Maniak003/Anemometer/Documents/16.png

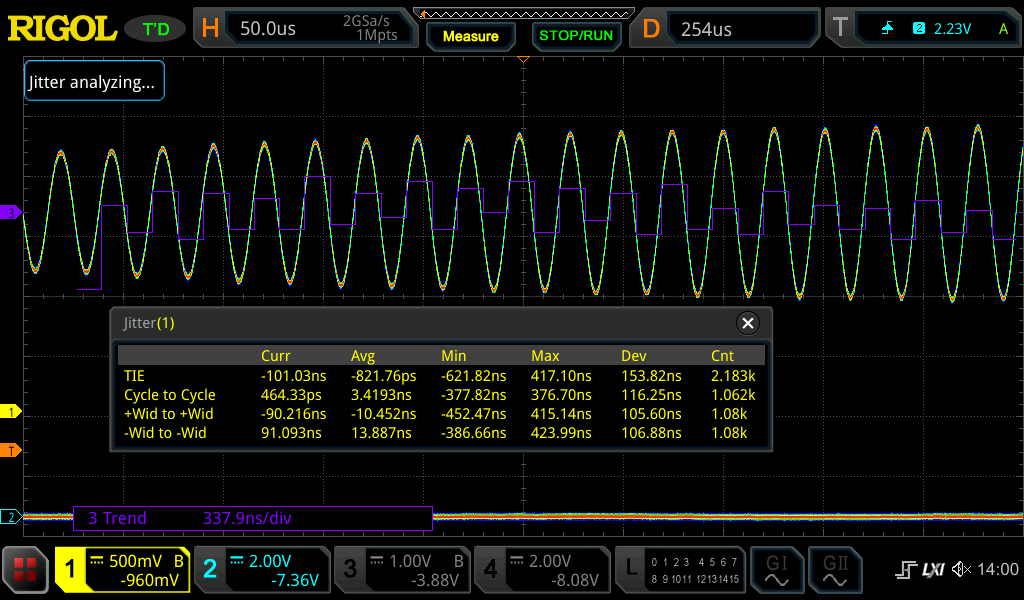
Documents/16.png
