Maniak003/Anemometer/Documents/29.png

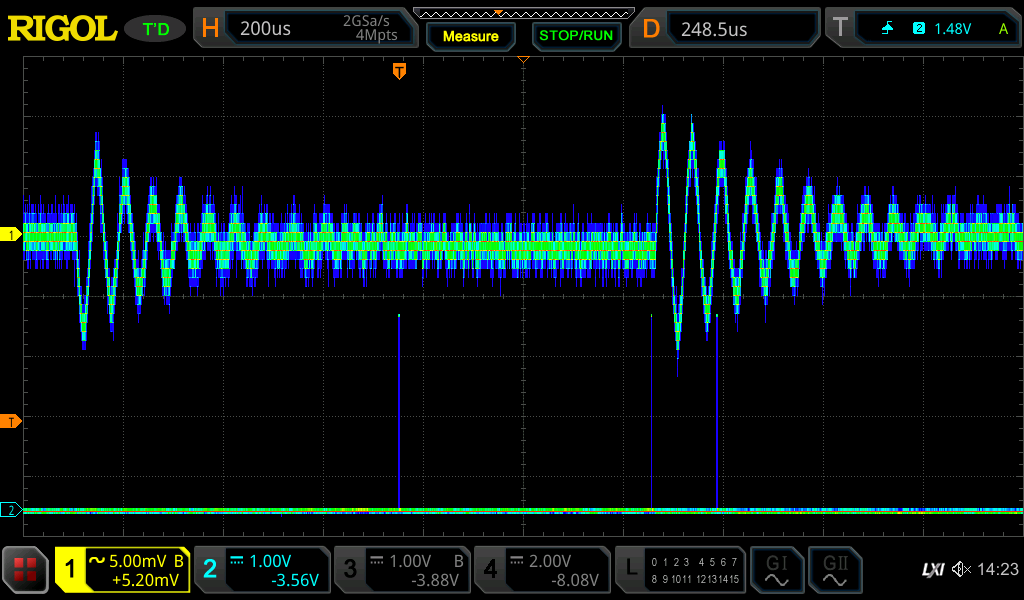
Documents/29.png
