Maniak003/Anemometer/Documents/34.png

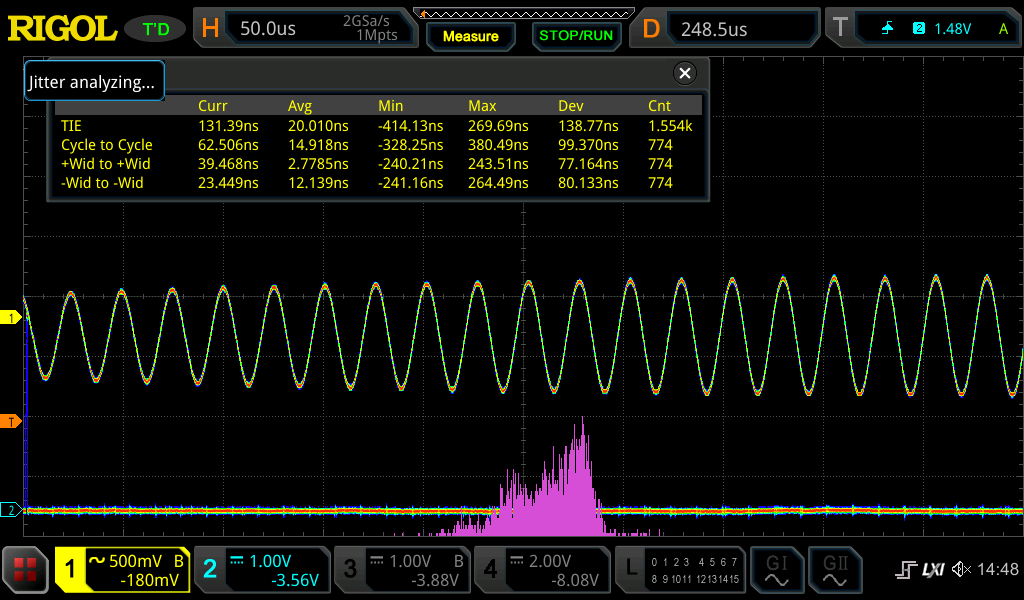
Documents/34.png
