Maniak003/Anemometer/Documents/63mm-Crystall_200khz.png

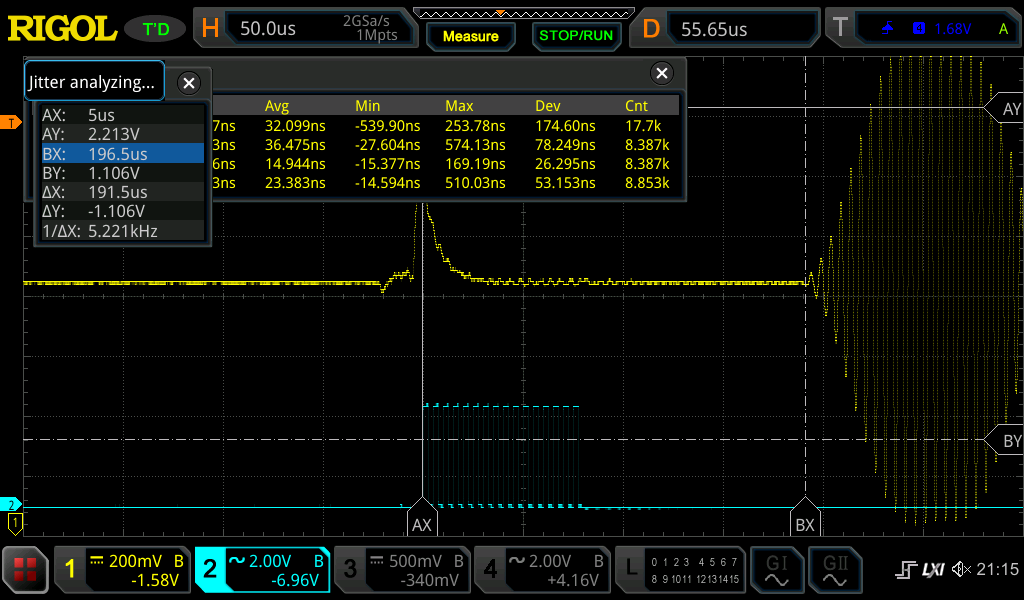
Documents/63mm-Crystall_200khz.png
