Maniak003/Anemometer/Documents/80.png

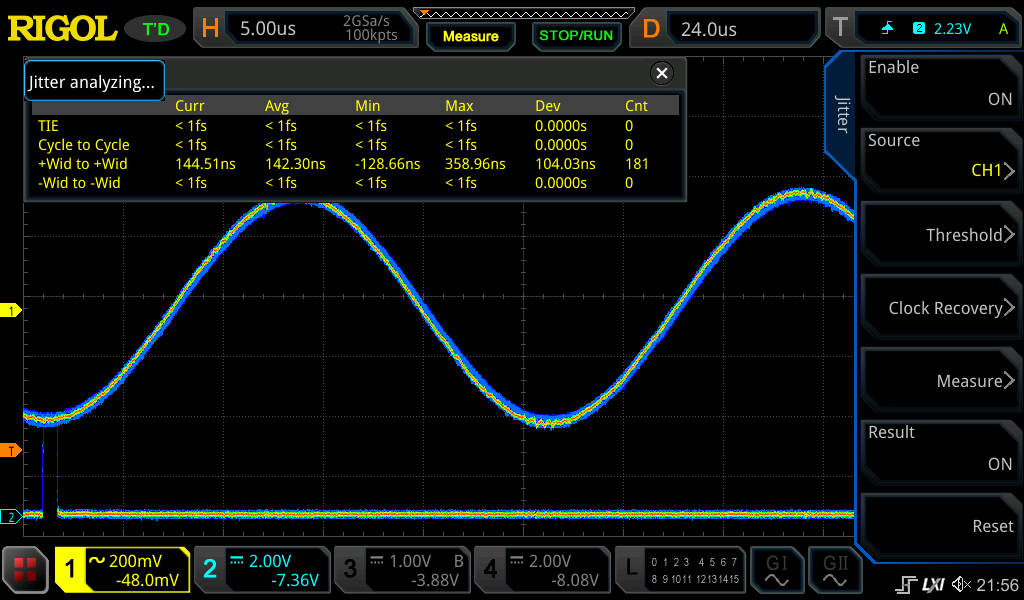
Documents/80.png
