Maniak003/Anemometer/Documents/200_conv.png

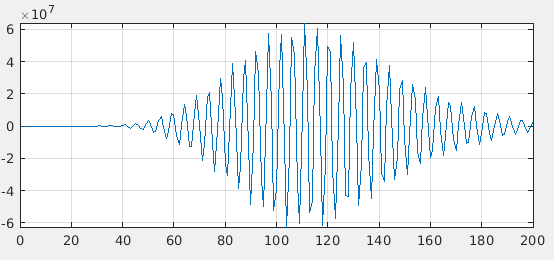
Documents/200_conv.png
