Maniak003/Anemometer/Documents/200_hilbert.png

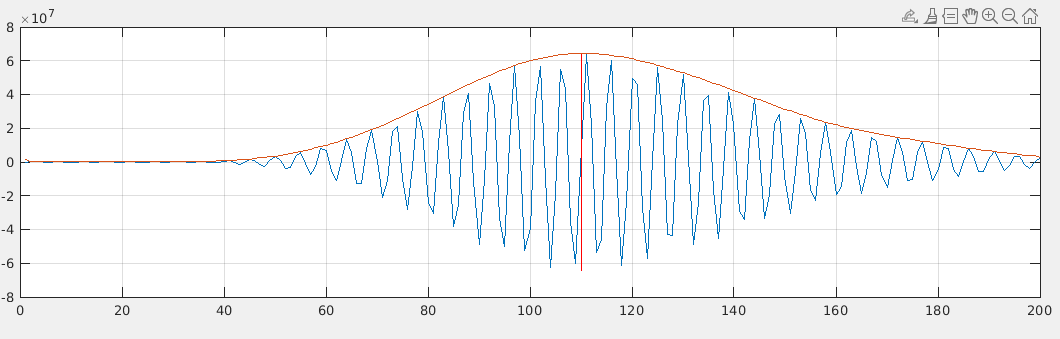
Documents/200_hilbert.png
