Maniak003/Anemometer/Documents/200_sample.png

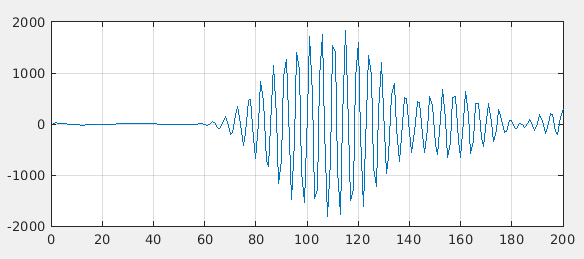
Documents/200_sample.png
