Maniak003/Anemometer/Documents/237.png

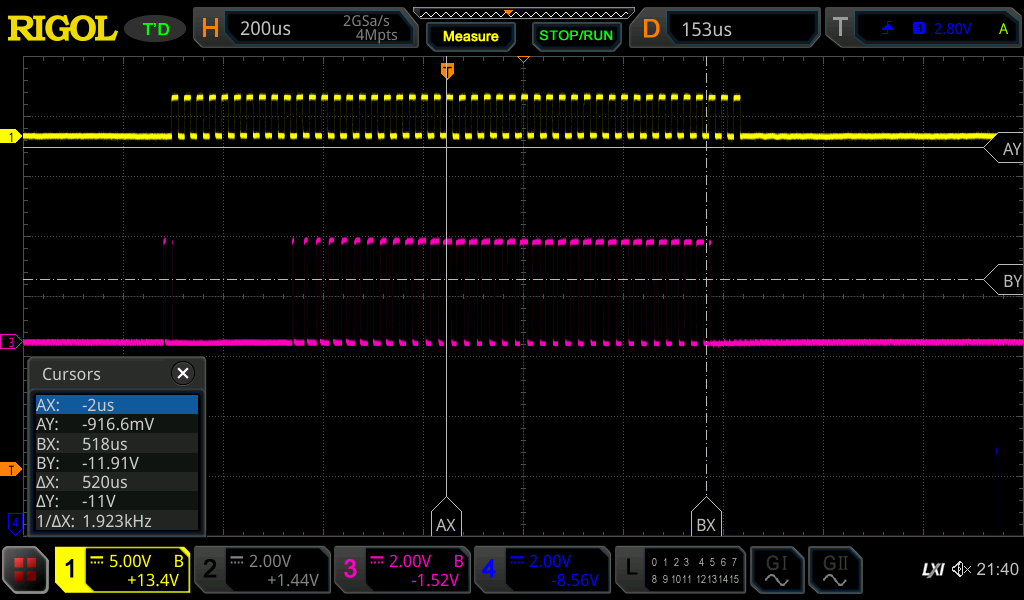
Documents/237.png
