Maniak003/Anemometer/Documents/344.png

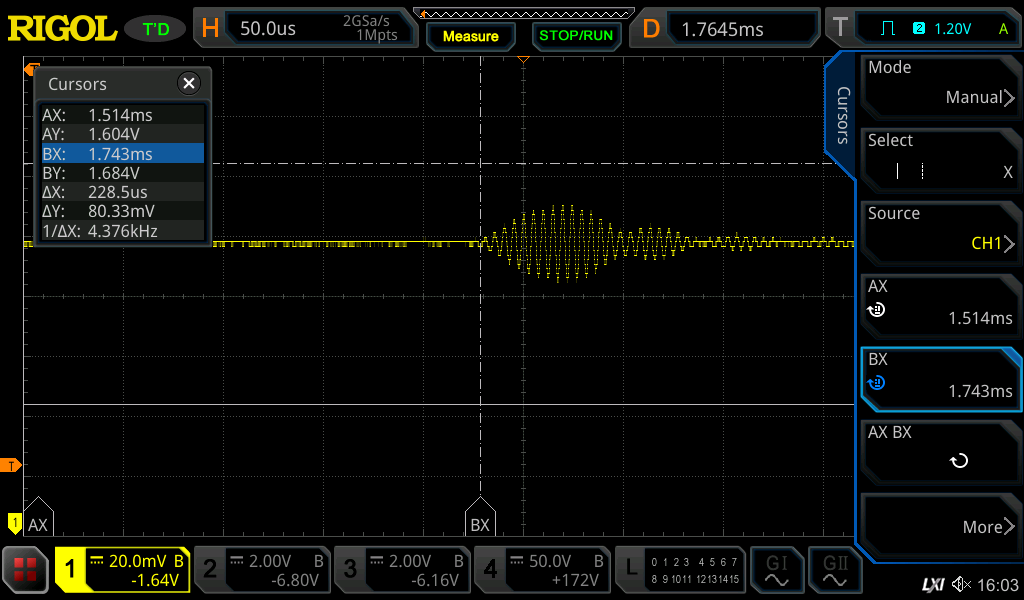
Documents/344.png
