Maniak003/Anemometer/Documents/406.png

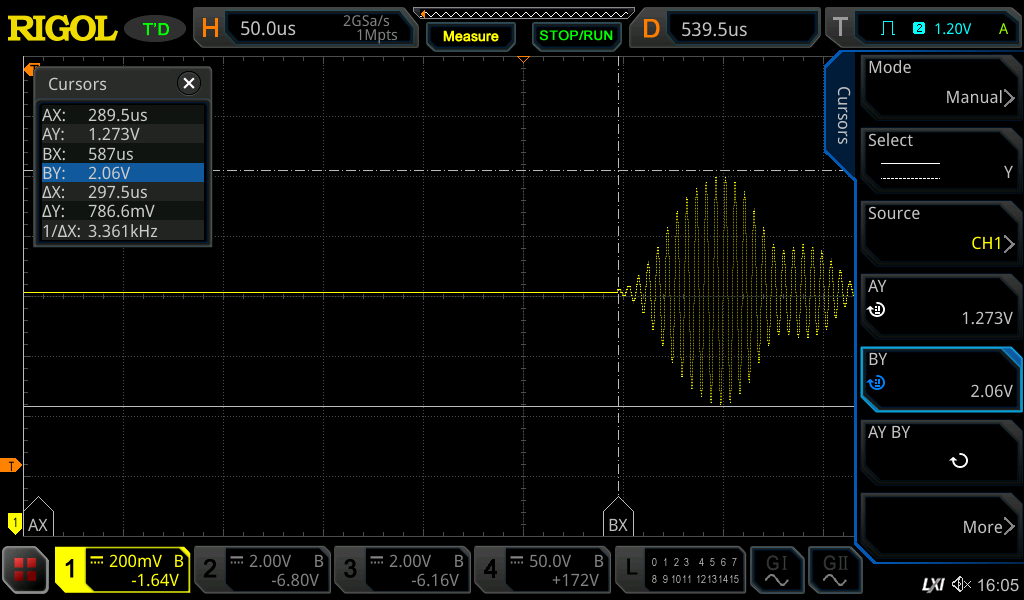
Documents/406.png
