Maniak003/Anemometer/Documents/476.png

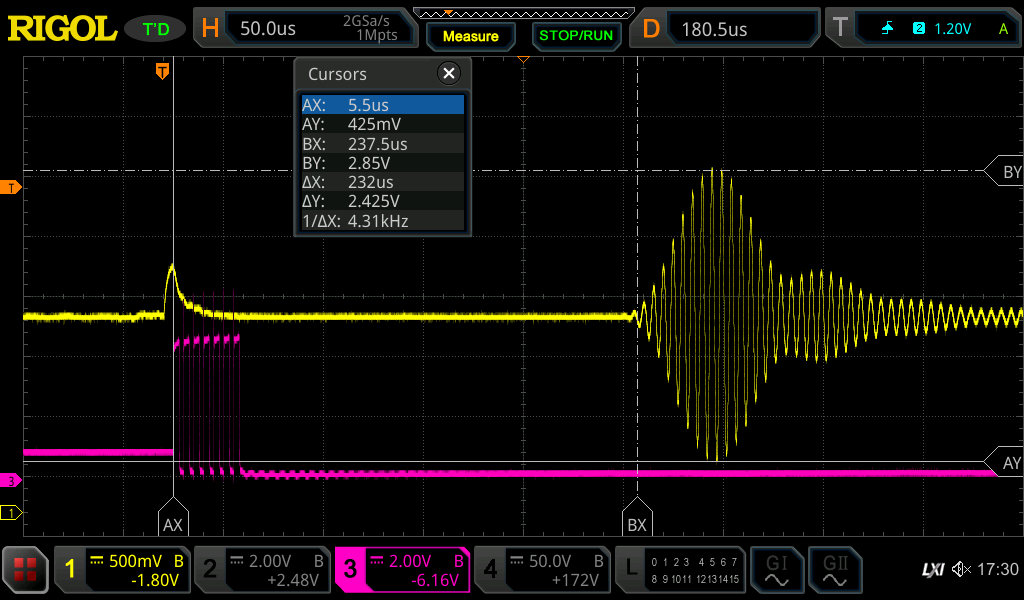
Documents/476.png
