Maniak003/Anemometer/Documents/572.png

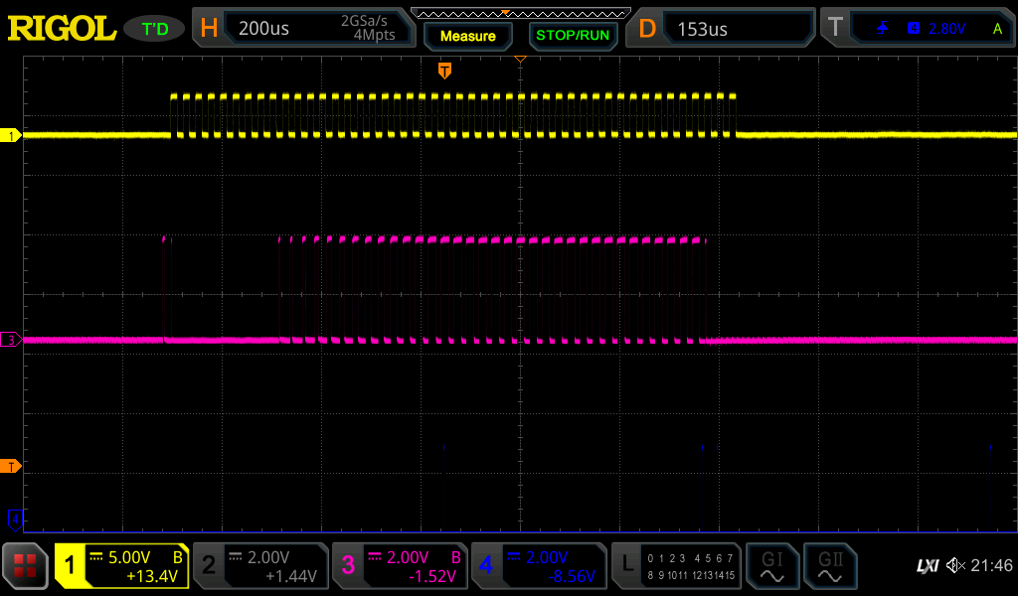
Documents/572.png
