Maniak003/Anemometer/Documents/635.png

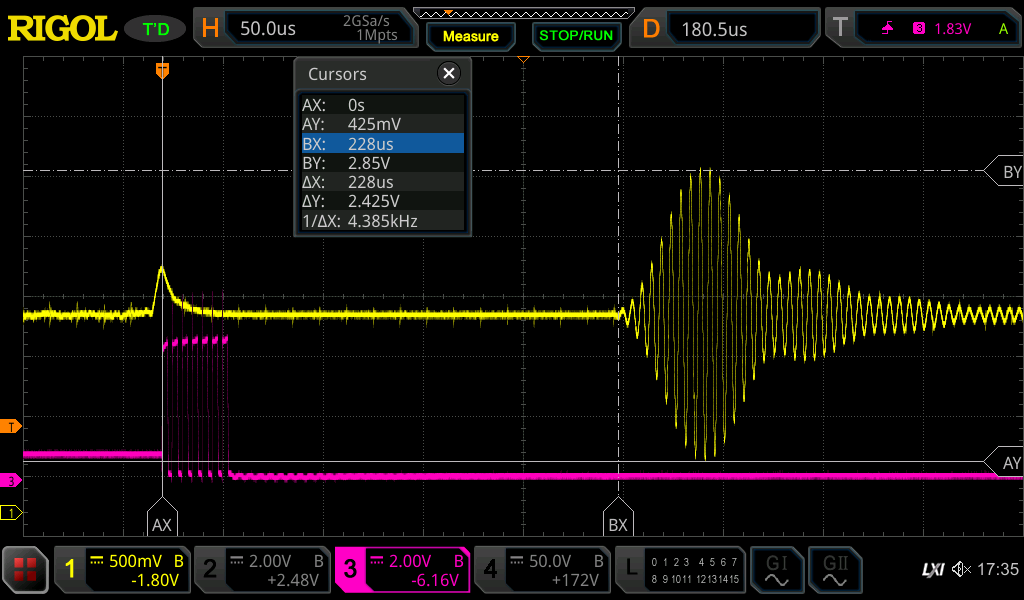
Documents/635.png
