Maniak003/Anemometer/Documents/1690.png

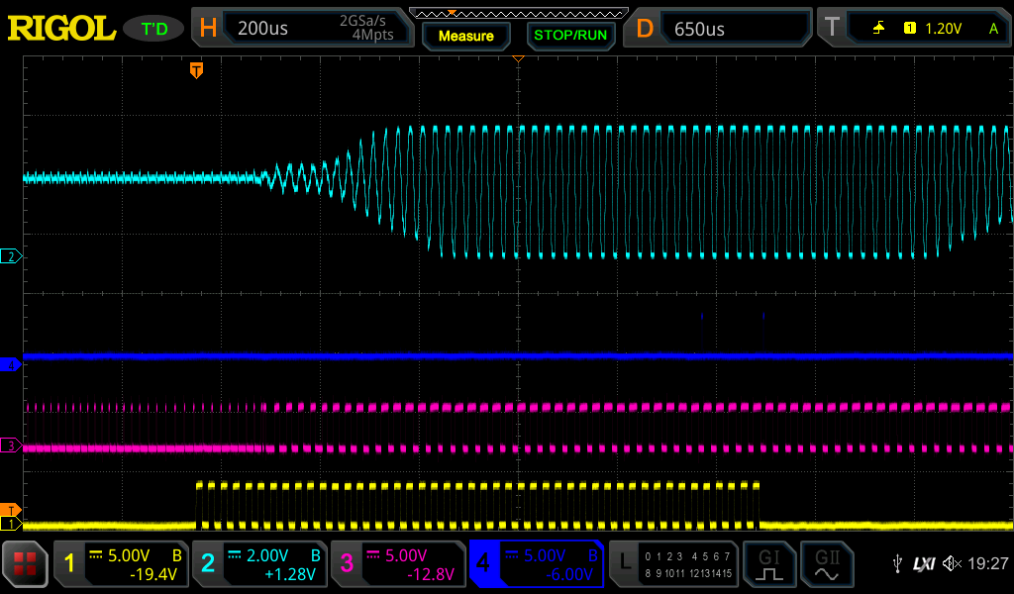
Documents/1690.png
