Maniak003/Anemometer/Documents/2022_04_03_20_00_22_110.png

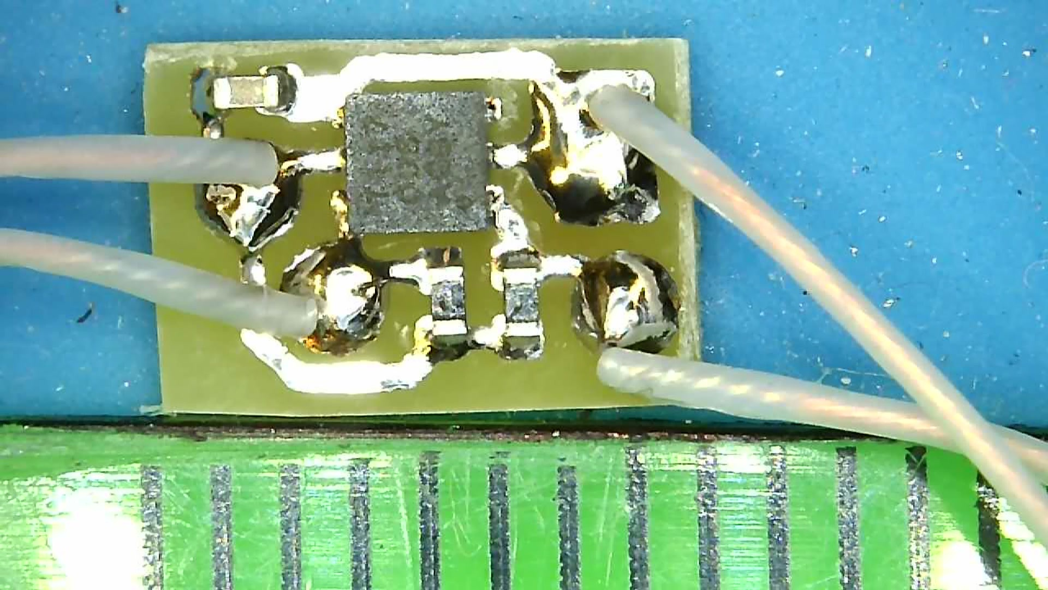
Documents/2022_04_03_20_00_22_110.png
