Maniak003/Anemometer/Documents/boardA.png

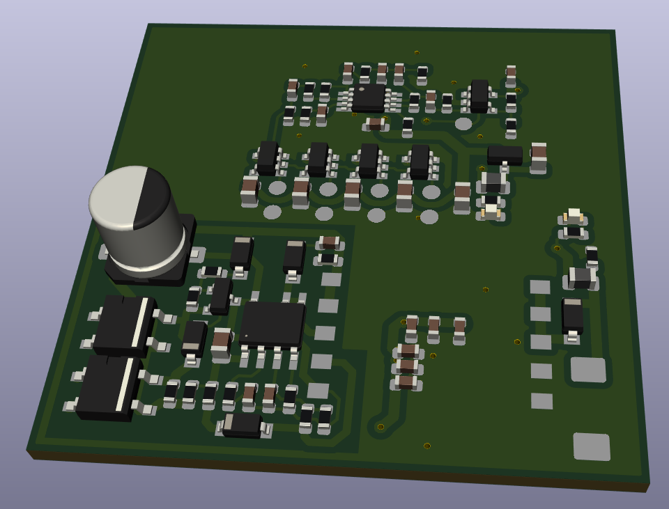
Documents/boardA.png
