Maniak003/Anemometer/Documents/boardB.png

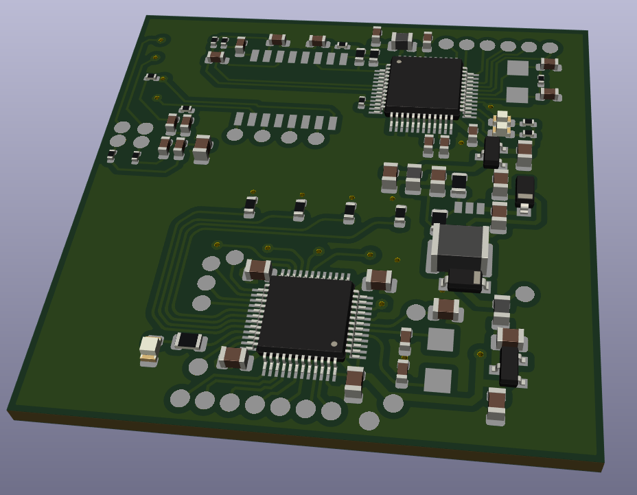
Documents/boardB.png
