Maniak003/Anemometer/Documents/Crystall-40kHz.png

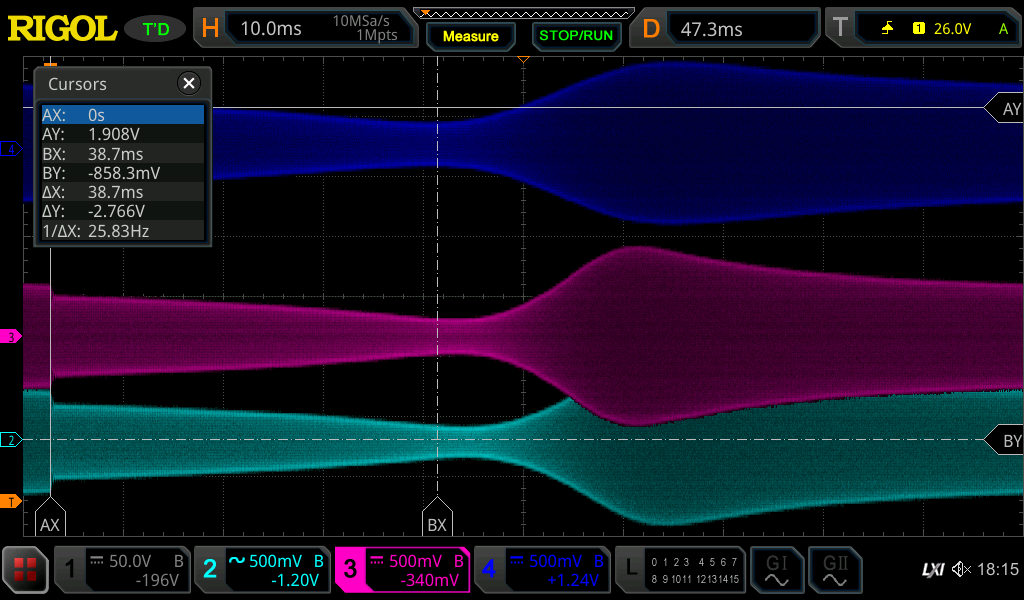
Documents/Crystall-40kHz.png
