Maniak003/Anemometer/Documents/Crystall_200khz.png

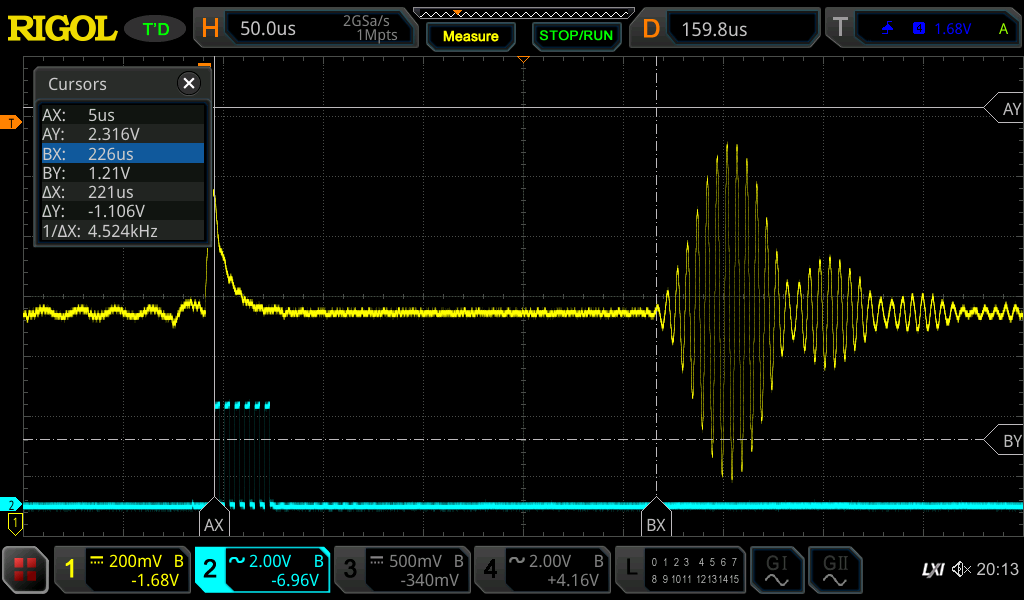
Documents/Crystall_200khz.png
