Maniak003/Anemometer/Documents/IMG_20220105_221915.jpg

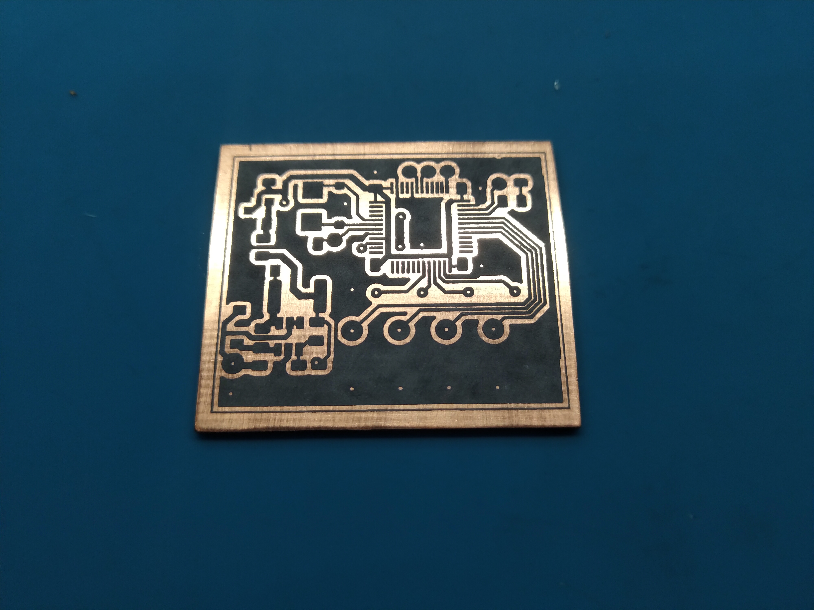
Documents/IMG_20220105_221915.jpg
