Maniak003/Anemometer/Documents/IMG_20220105_221929.jpg

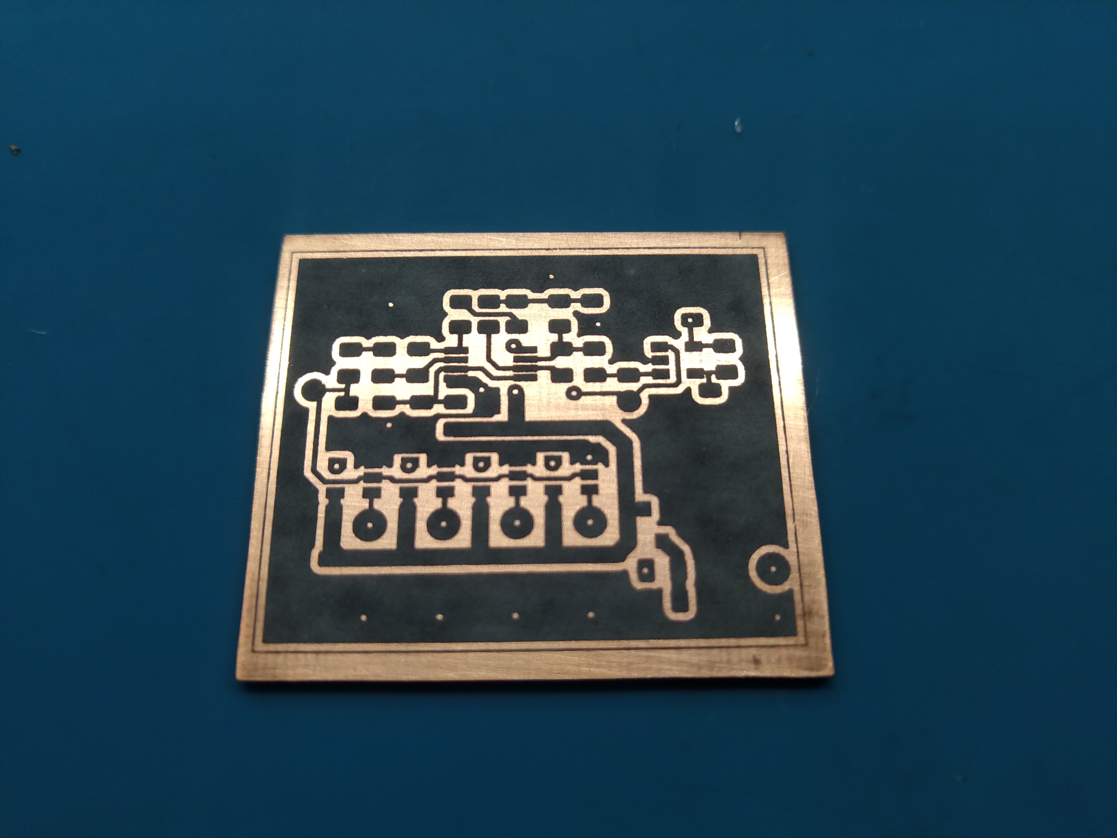
Documents/IMG_20220105_221929.jpg
