Maniak003/Anemometer/Documents/IMG_20220106_001547.jpg

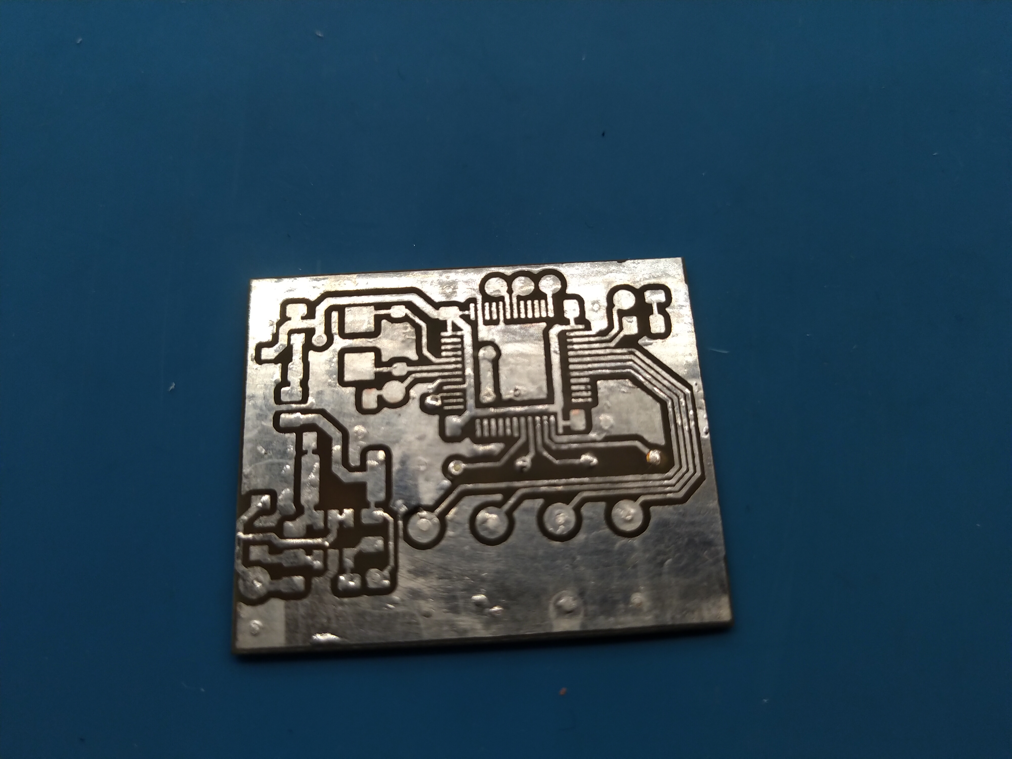
Documents/IMG_20220106_001547.jpg
