Maniak003/Anemometer/Documents/IMG_20220106_001603.jpg

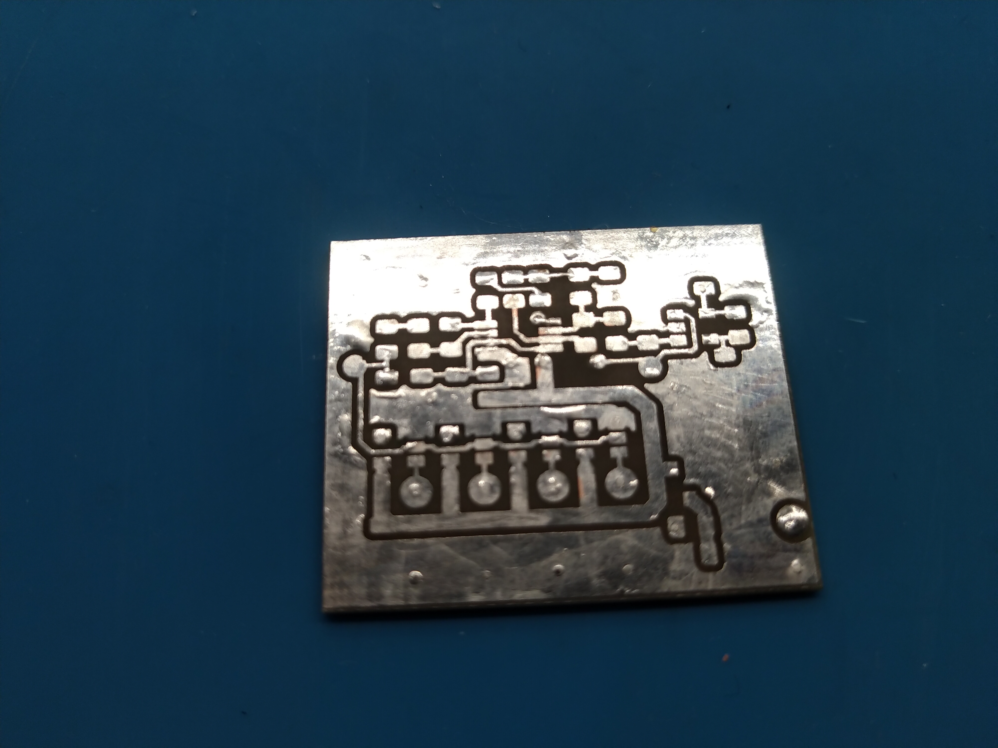
Documents/IMG_20220106_001603.jpg
