Maniak003/Anemometer/Documents/IMG_20220202_125025.jpg

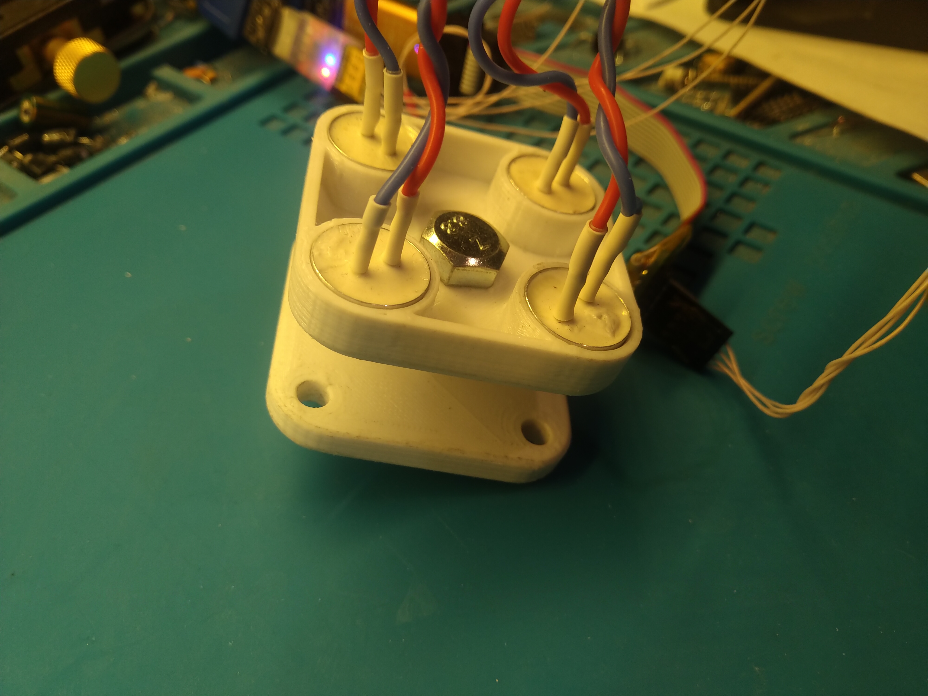
Documents/IMG_20220202_125025.jpg
