Maniak003/Anemometer/Documents/IMG_20220202_125037.jpg

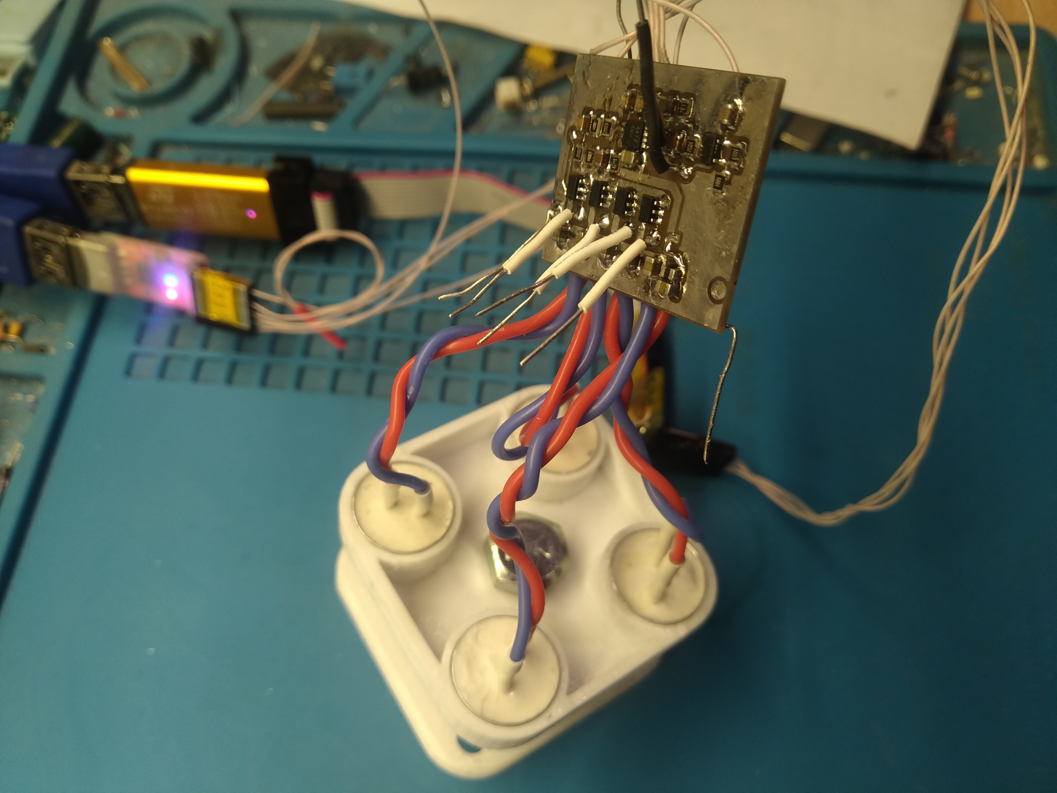
Documents/IMG_20220202_125037.jpg
