Maniak003/Anemometer/Documents/IMG_20220220_214210.jpg

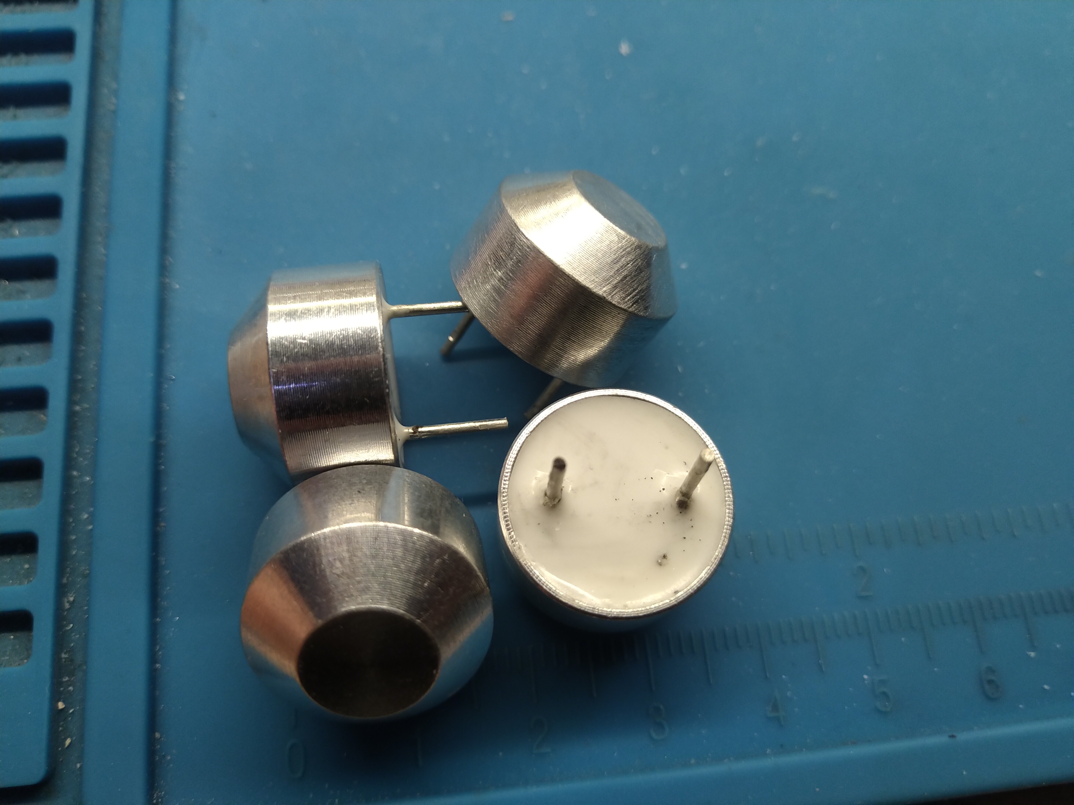
Documents/IMG_20220220_214210.jpg
