Maniak003/Anemometer/Documents/IMG_20220308_124159.jpg

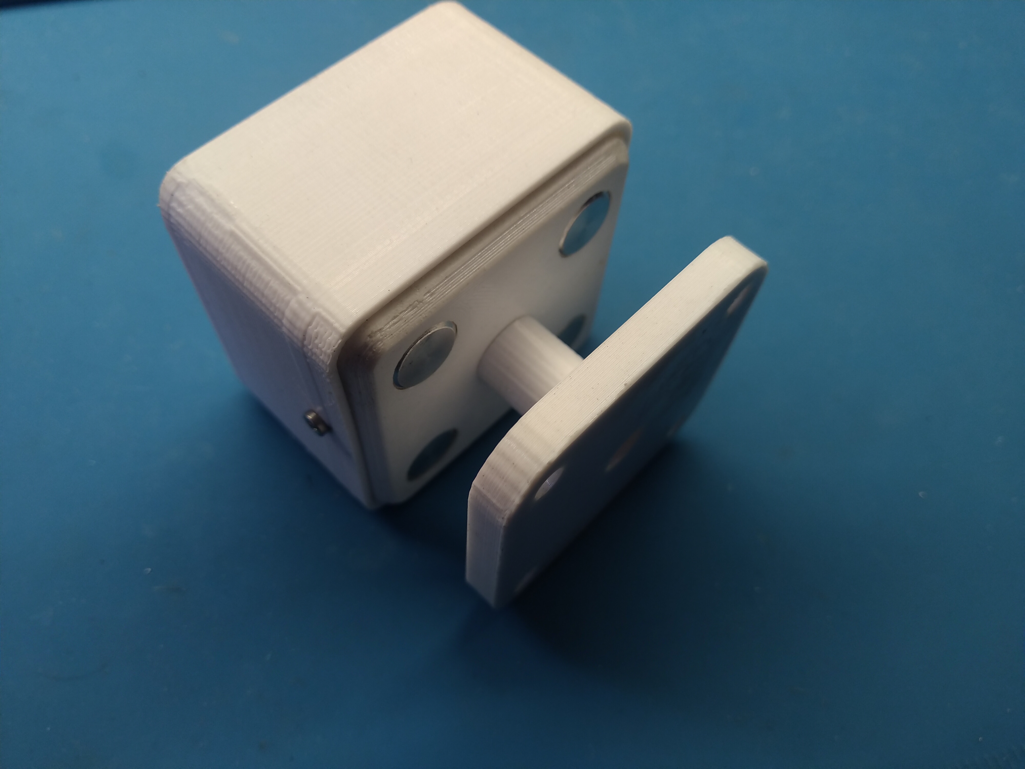
Documents/IMG_20220308_124159.jpg
