Maniak003/Anemometer/Documents/IMG_20220320_121318.jpg

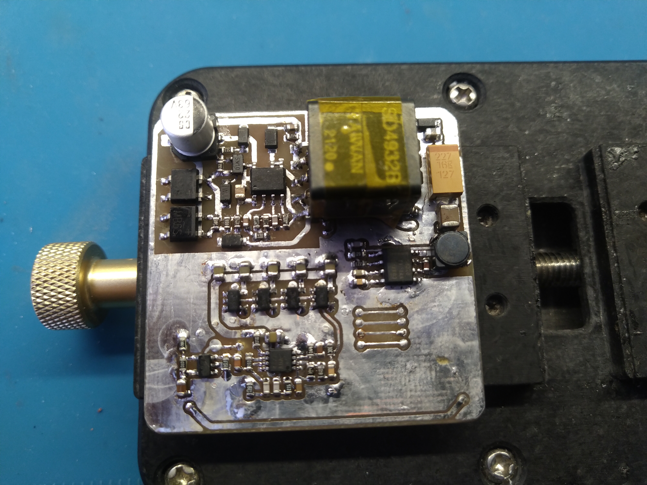
Documents/IMG_20220320_121318.jpg
