Maniak003/Anemometer/Documents/IMG_20220320_154554.jpg

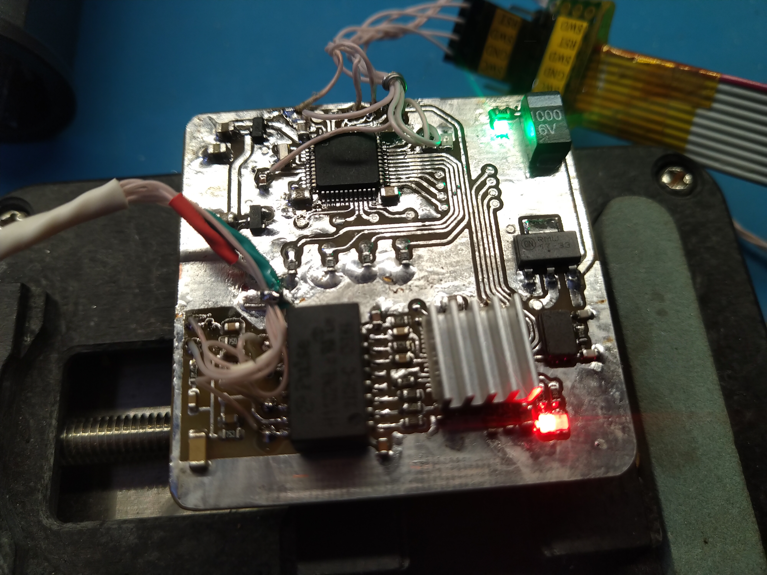
Documents/IMG_20220320_154554.jpg
