Maniak003/Anemometer/Documents/IMG_20220403_183047.jpg

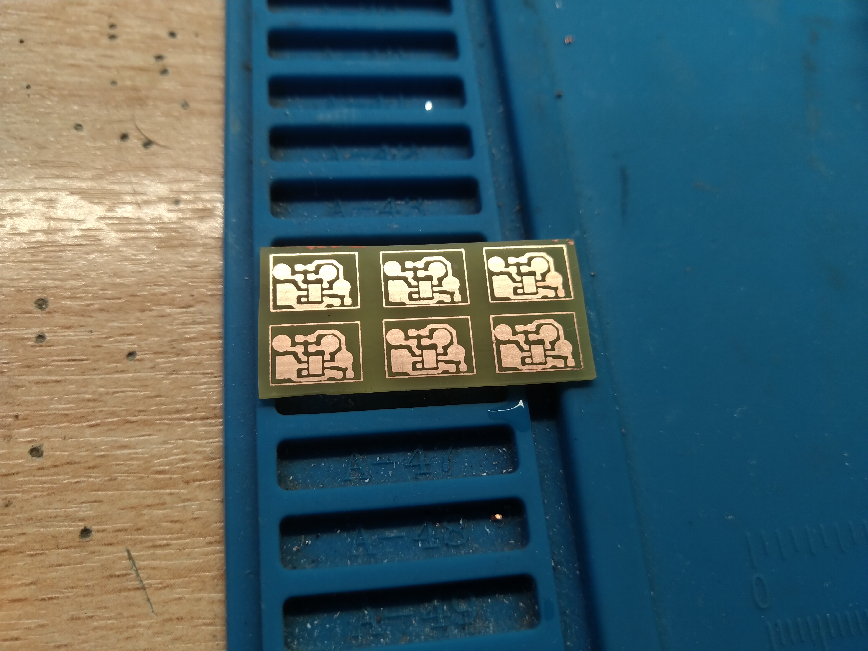
Documents/IMG_20220403_183047.jpg
