Maniak003/Anemometer/Documents/IMG_20220410_160630.jpg

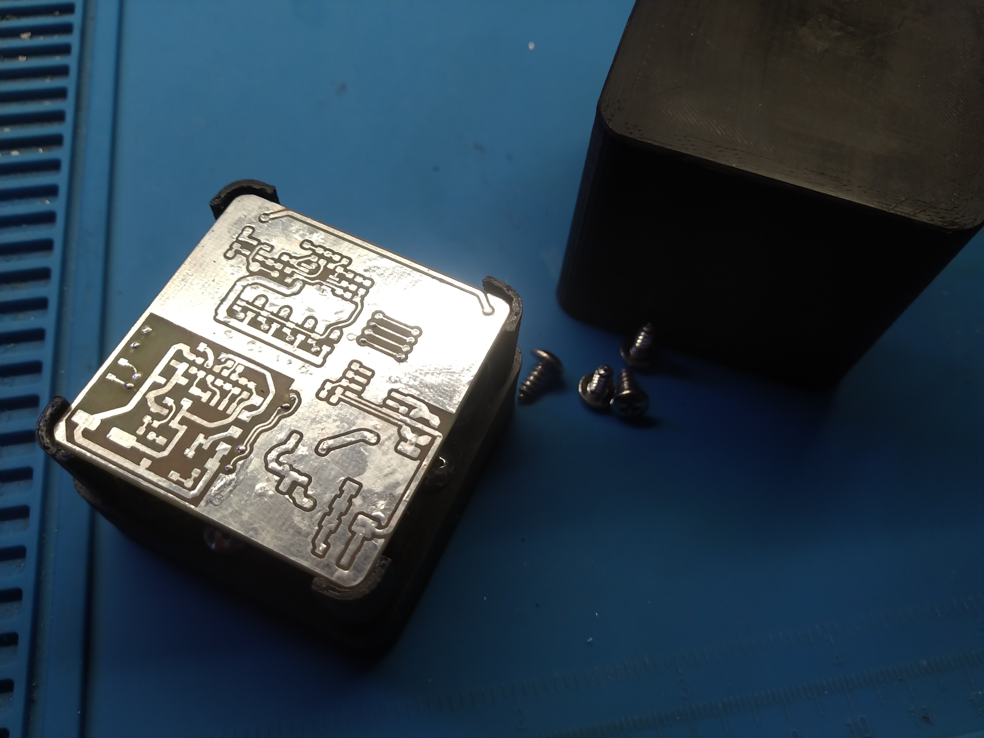
Documents/IMG_20220410_160630.jpg
