Maniak003/Anemometer/Documents/IMG_20220414_123952.jpg

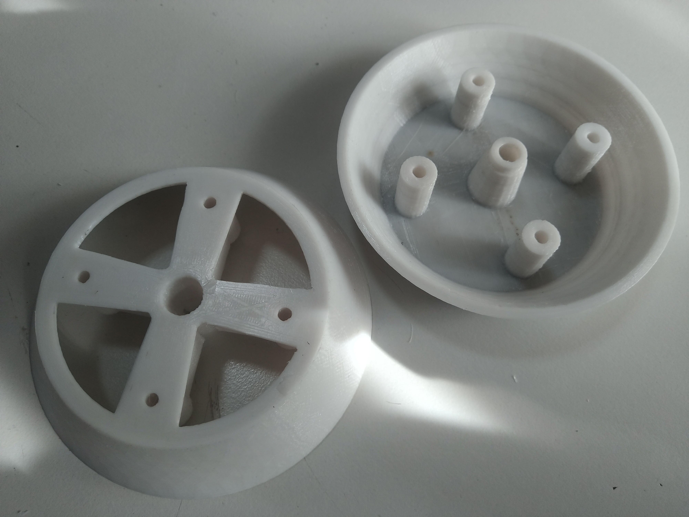
Documents/IMG_20220414_123952.jpg
