Maniak003/Anemometer/Documents/IMG_20220415_115337.jpg

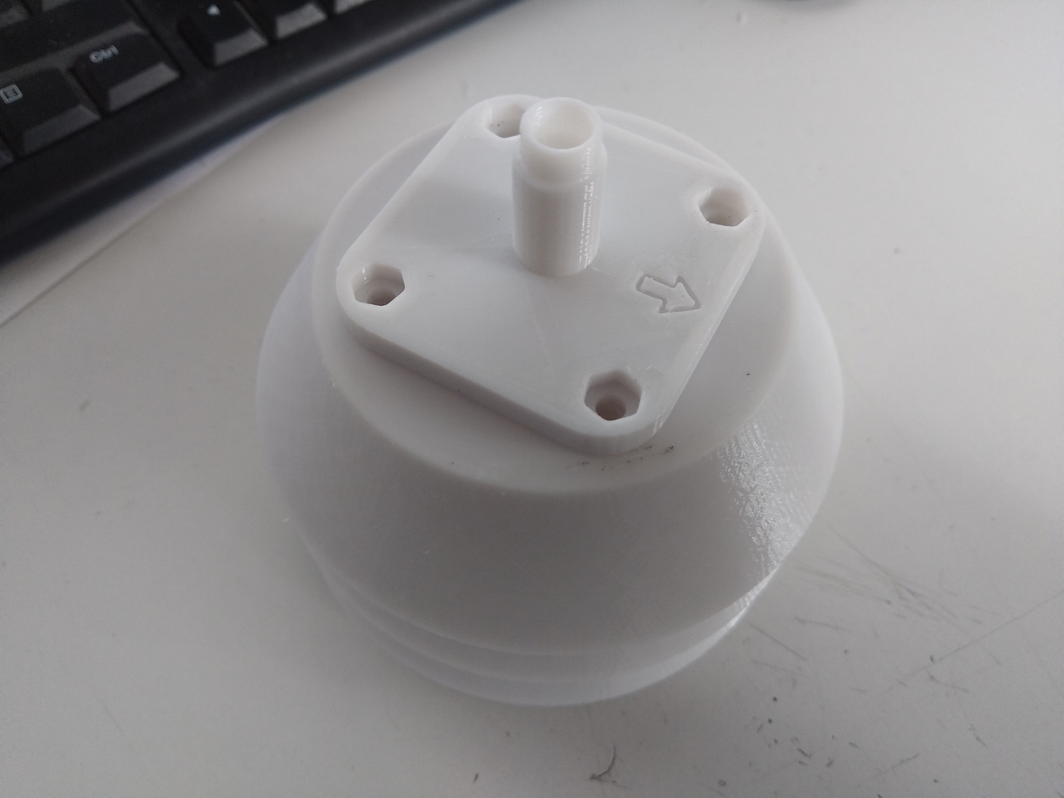
Documents/IMG_20220415_115337.jpg
