Maniak003/Anemometer/Documents/IMG_20220415_115925.jpg

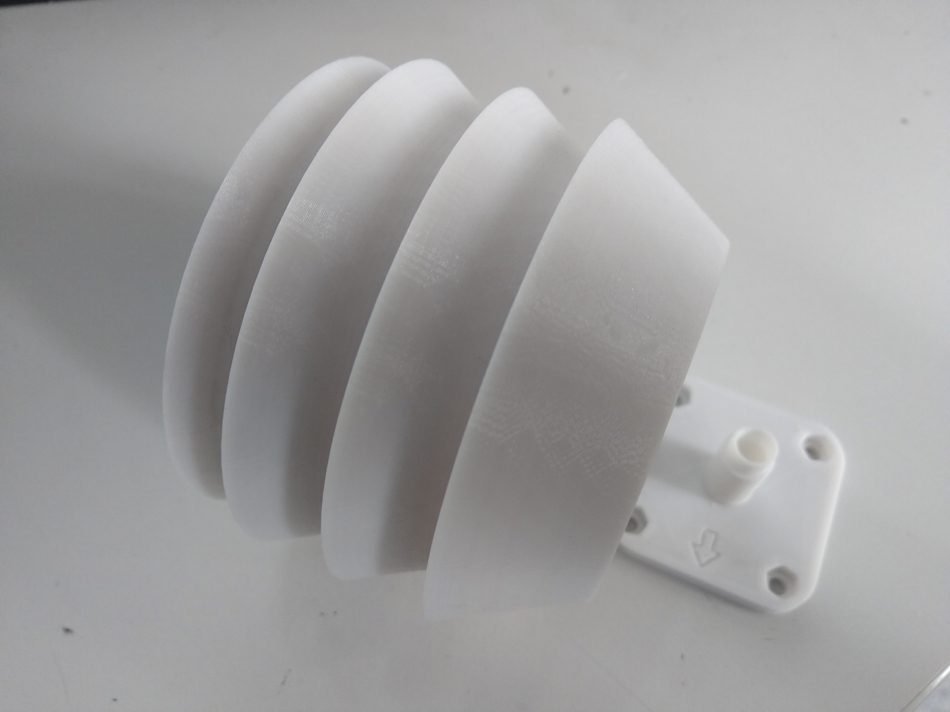
Documents/IMG_20220415_115925.jpg
