Maniak003/Anemometer/Documents/IMG_20220415_115932.jpg

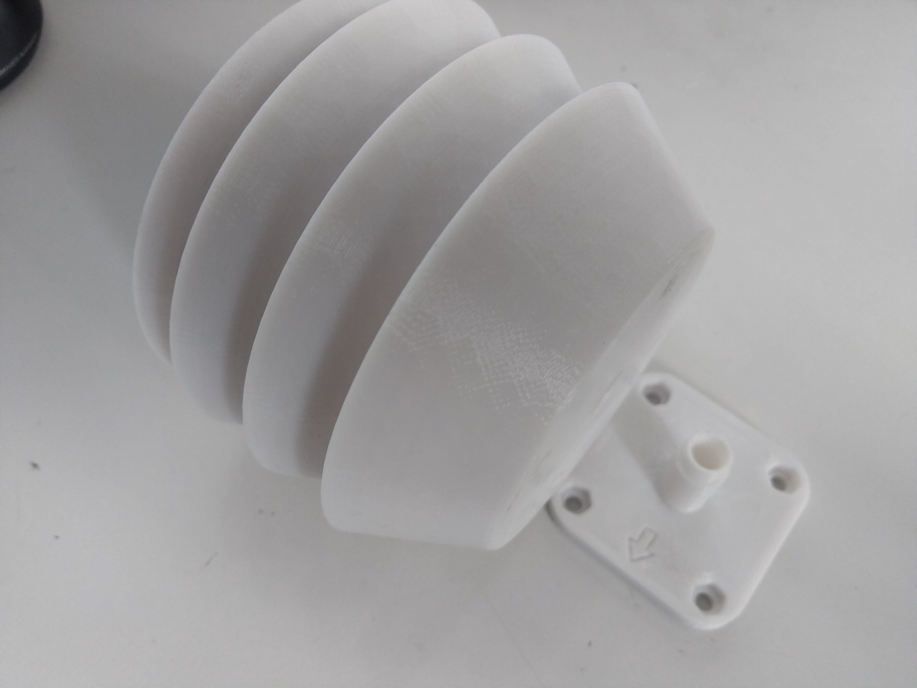
Documents/IMG_20220415_115932.jpg
