Maniak003/Anemometer/Documents/IMG_20220416_165911.jpg

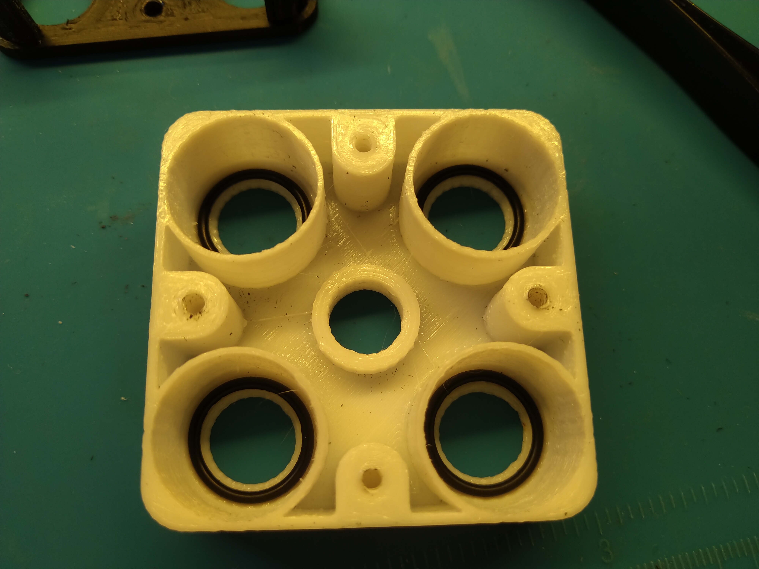
Documents/IMG_20220416_165911.jpg
