Maniak003/Anemometer/Documents/IMG_20220416_171755.jpg

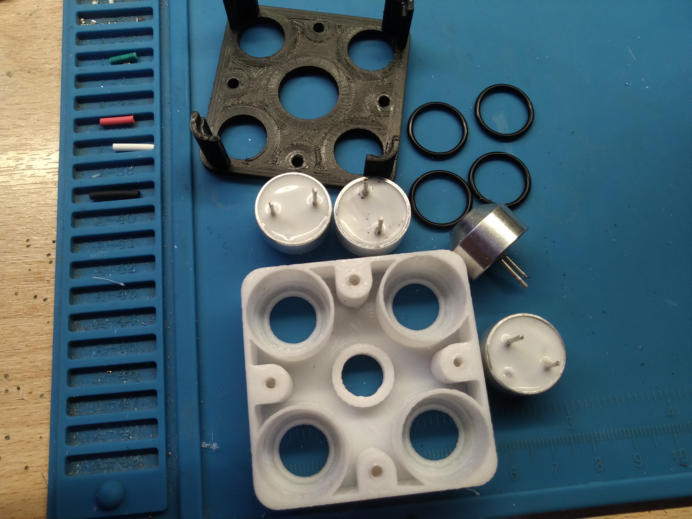
Documents/IMG_20220416_171755.jpg
