Maniak003/Anemometer/Documents/IMG_20220416_171856.jpg

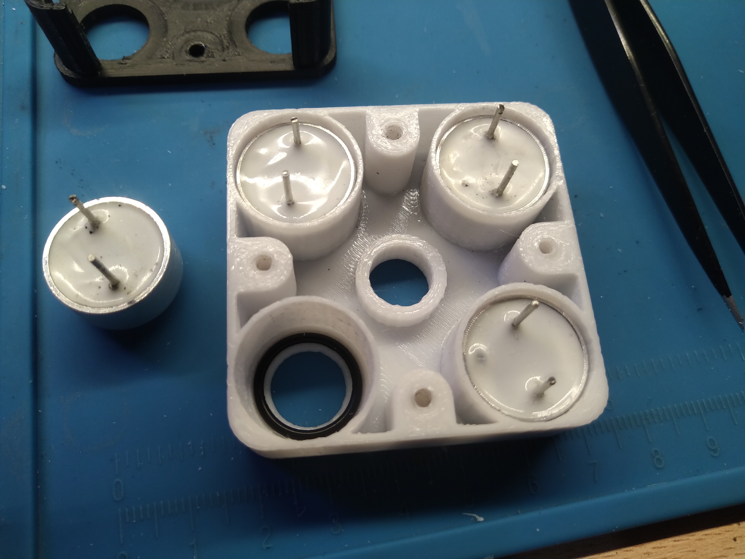
Documents/IMG_20220416_171856.jpg
