Maniak003/Anemometer/Documents/IMG_20220416_172011.jpg

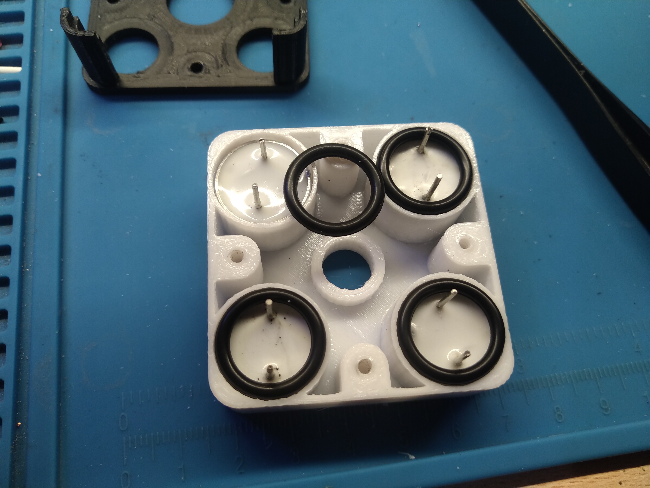
Documents/IMG_20220416_172011.jpg
