Maniak003/Anemometer/Documents/IMG_20220416_172027.jpg

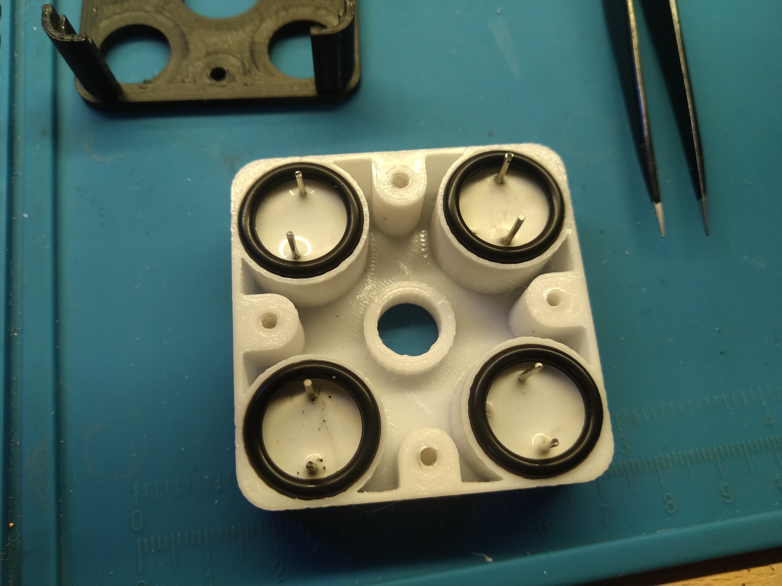
Documents/IMG_20220416_172027.jpg
