Maniak003/Anemometer/Documents/IMG_20220416_172209.jpg

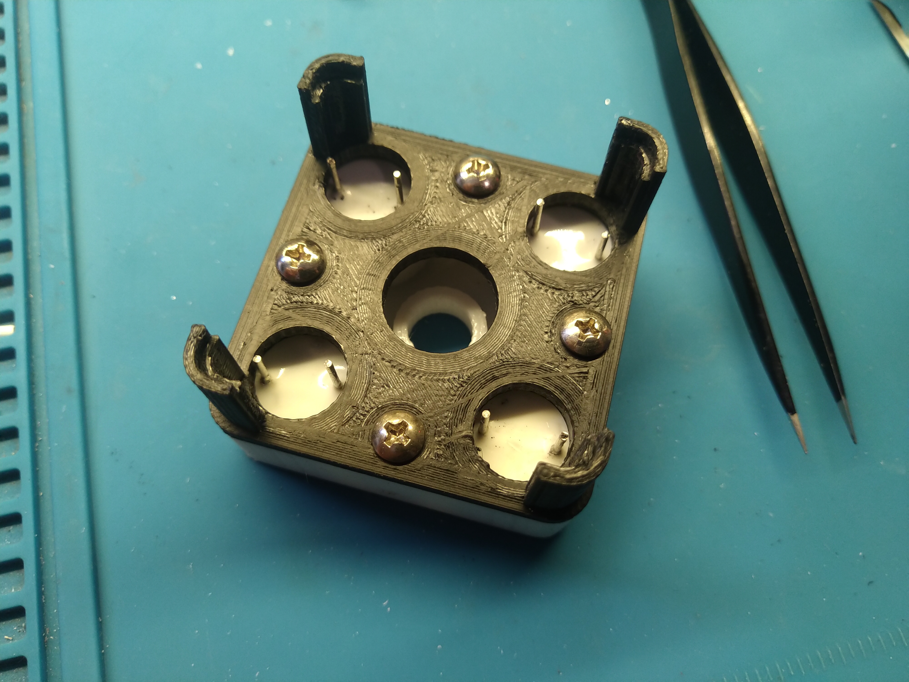
Documents/IMG_20220416_172209.jpg
