Maniak003/Anemometer/Documents/IMG_20220416_172220.jpg

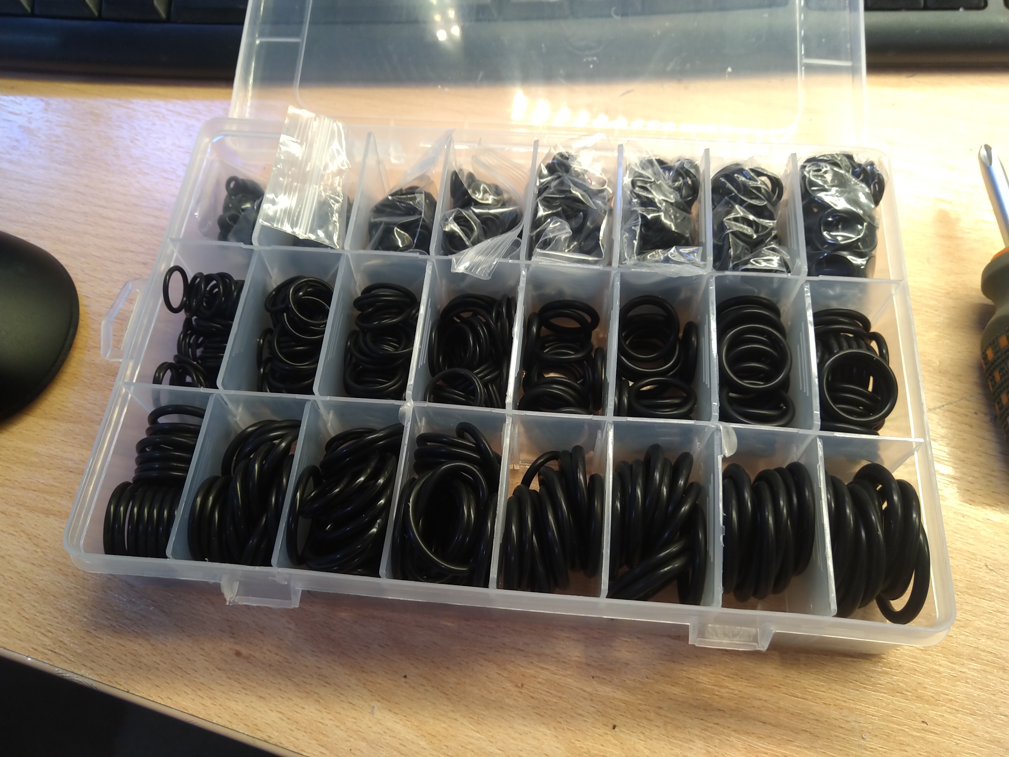
Documents/IMG_20220416_172220.jpg
