Maniak003/Anemometer/Documents/IMG_20220416_172407.jpg

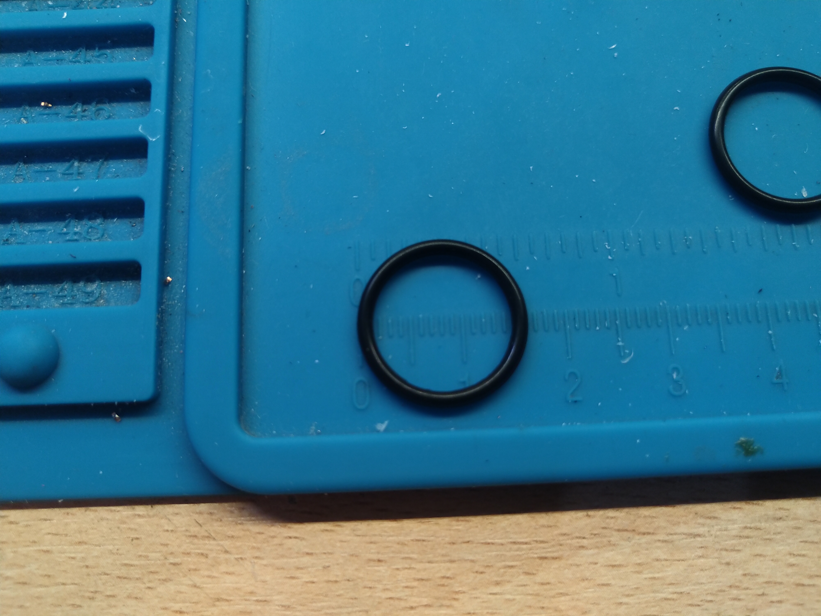
Documents/IMG_20220416_172407.jpg
