Maniak003/Anemometer/Documents/IMG_20220416_172509.jpg

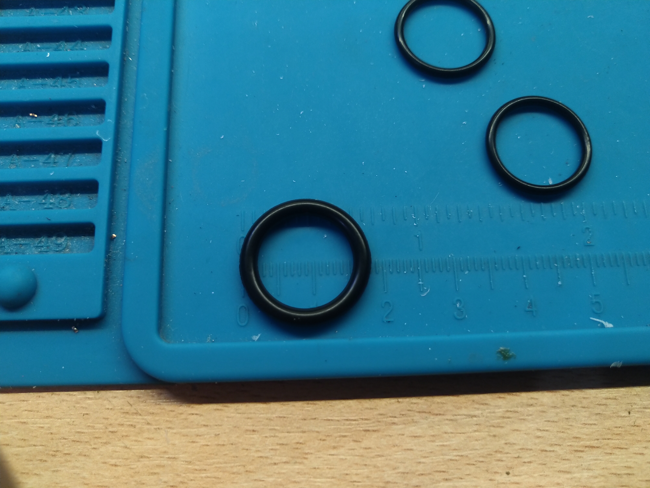
Documents/IMG_20220416_172509.jpg
