Maniak003/Anemometer/Documents/IMG_20220416_172617.jpg

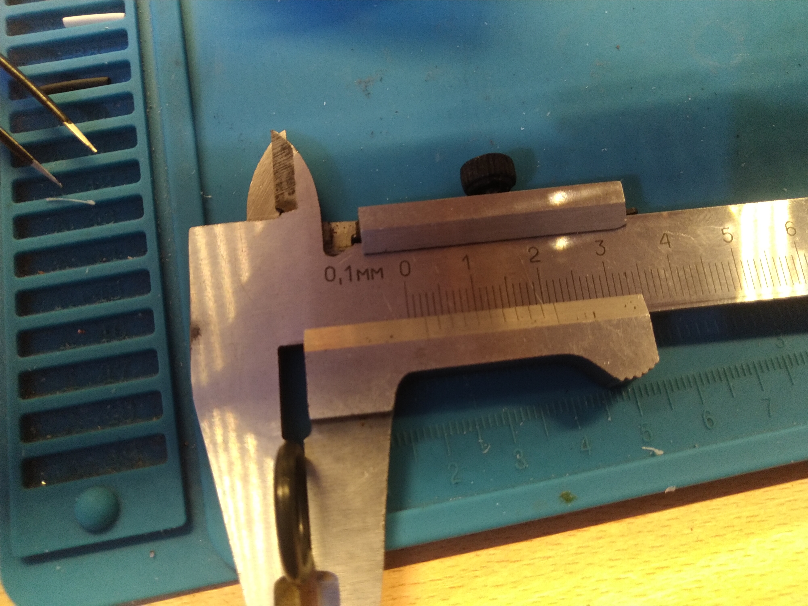
Documents/IMG_20220416_172617.jpg
