Maniak003/Anemometer/Documents/IMG_20220416_172658.jpg

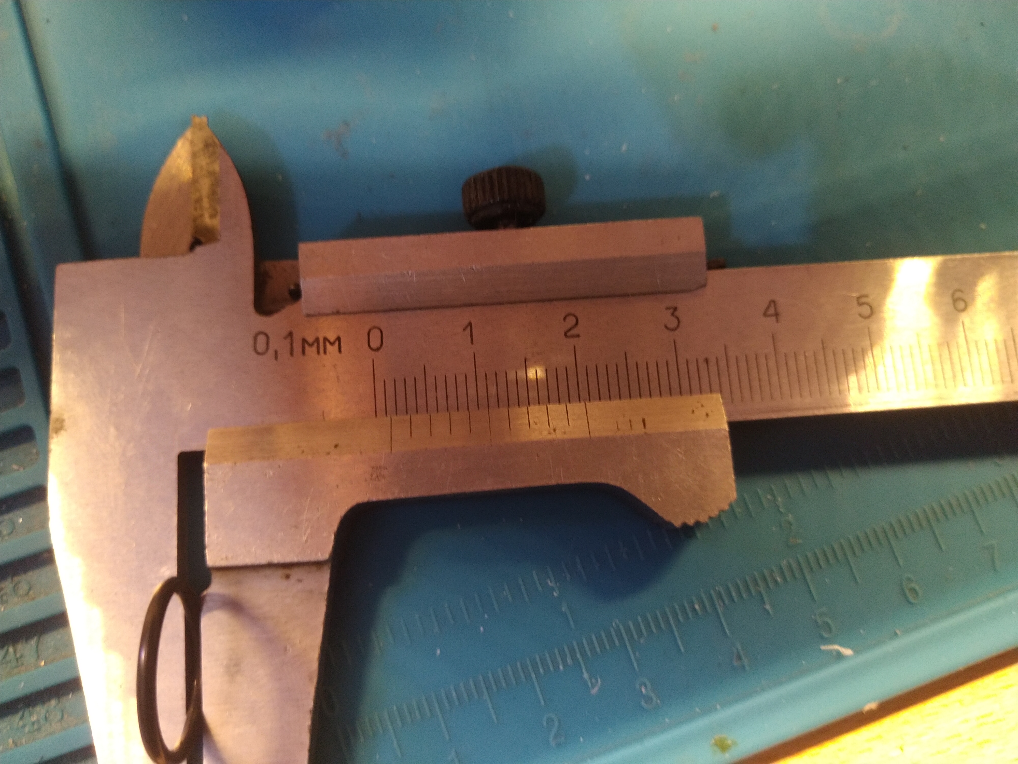
Documents/IMG_20220416_172658.jpg
