Maniak003/Anemometer/Documents/IMG_20220416_172824.jpg

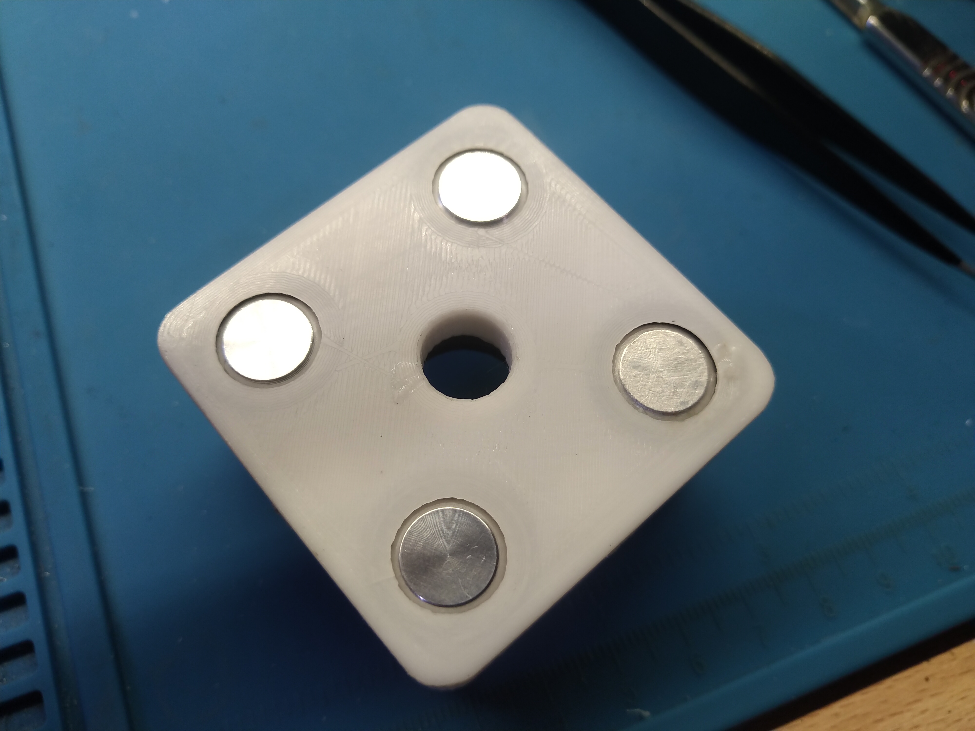
Documents/IMG_20220416_172824.jpg
