Maniak003/Anemometer/Documents/IMG_20220416_180539.jpg

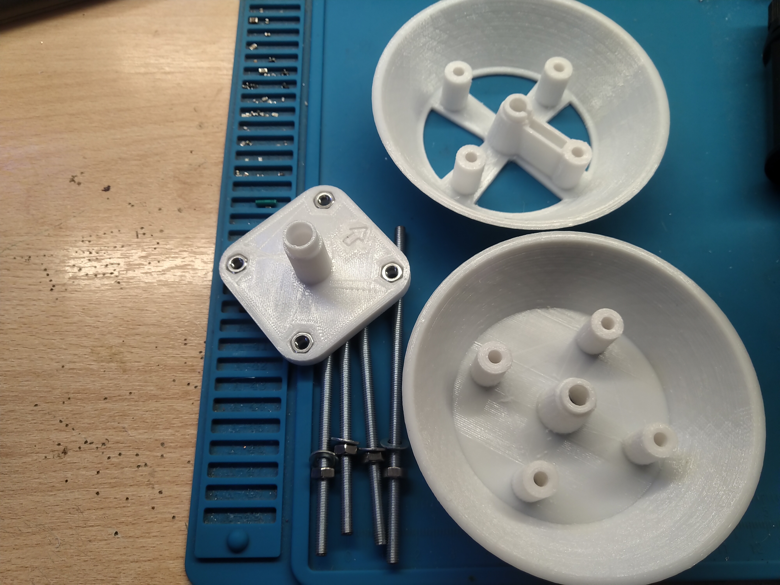
Documents/IMG_20220416_180539.jpg
