Maniak003/Anemometer/Documents/IMG_20220416_182753.jpg

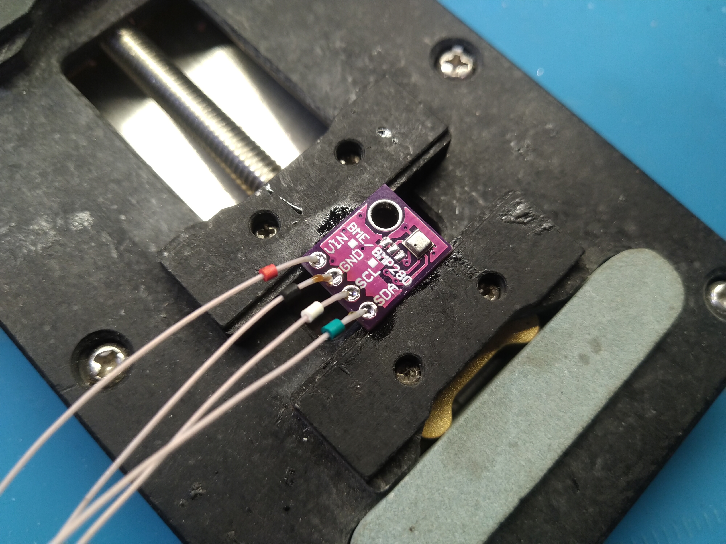
Documents/IMG_20220416_182753.jpg
