Maniak003/Anemometer/Documents/IMG_20220416_183042.jpg

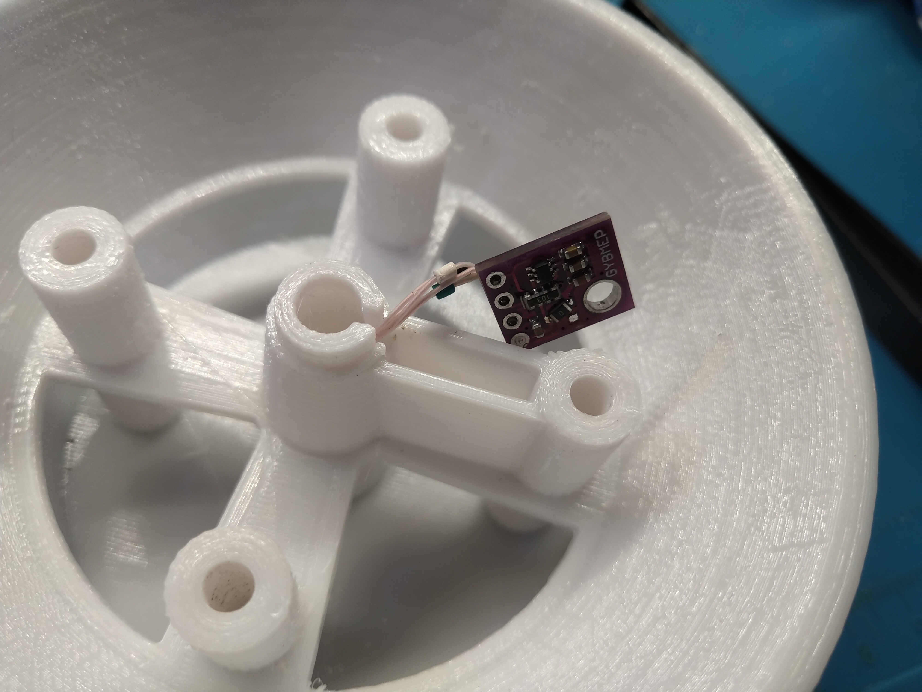
Documents/IMG_20220416_183042.jpg
