Maniak003/Anemometer/Documents/IMG_20220416_184421.jpg

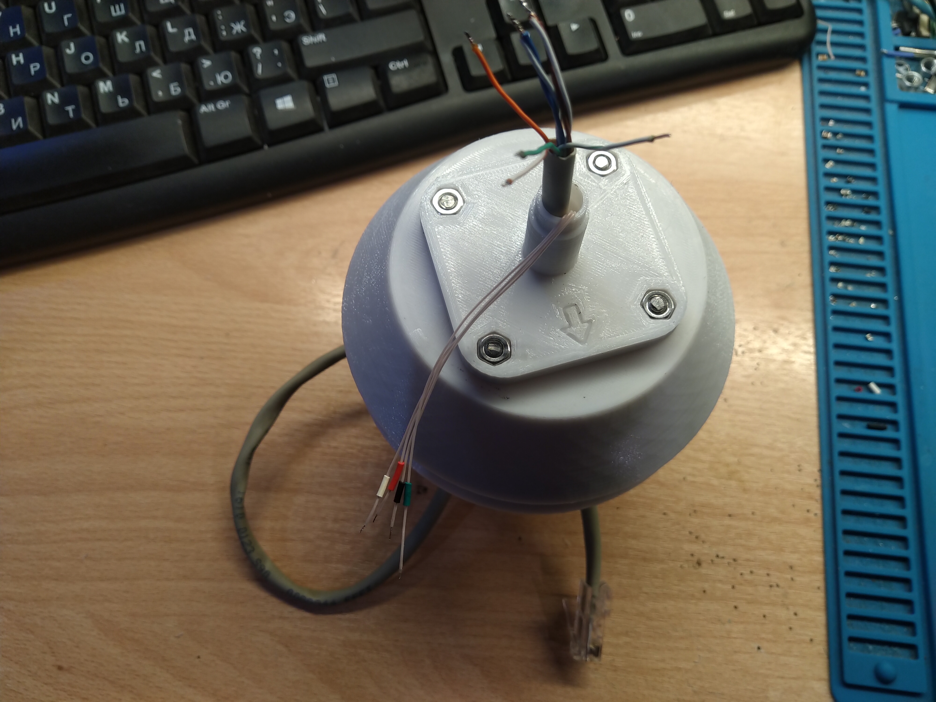
Documents/IMG_20220416_184421.jpg
