Maniak003/Anemometer/Documents/IMG_20230115_220432.jpg

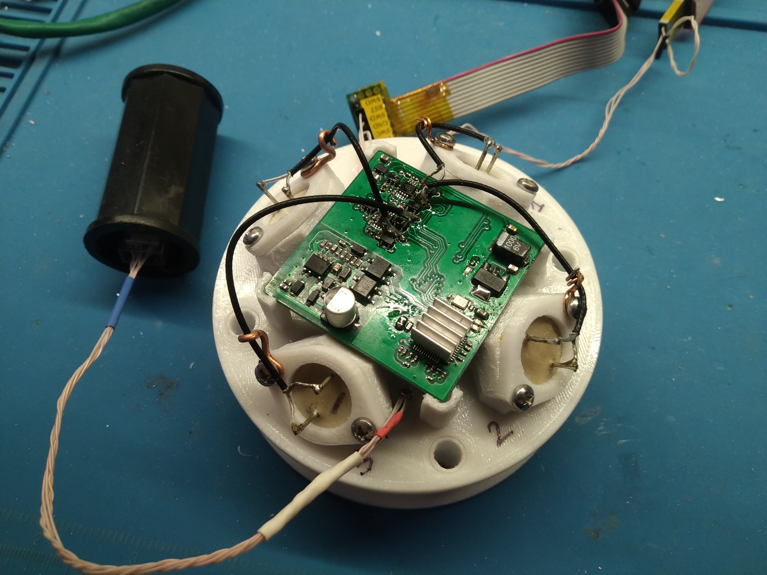
Documents/IMG_20230115_220432.jpg
