Maniak003/Anemometer/Documents/IMG_20230122_133305.jpg

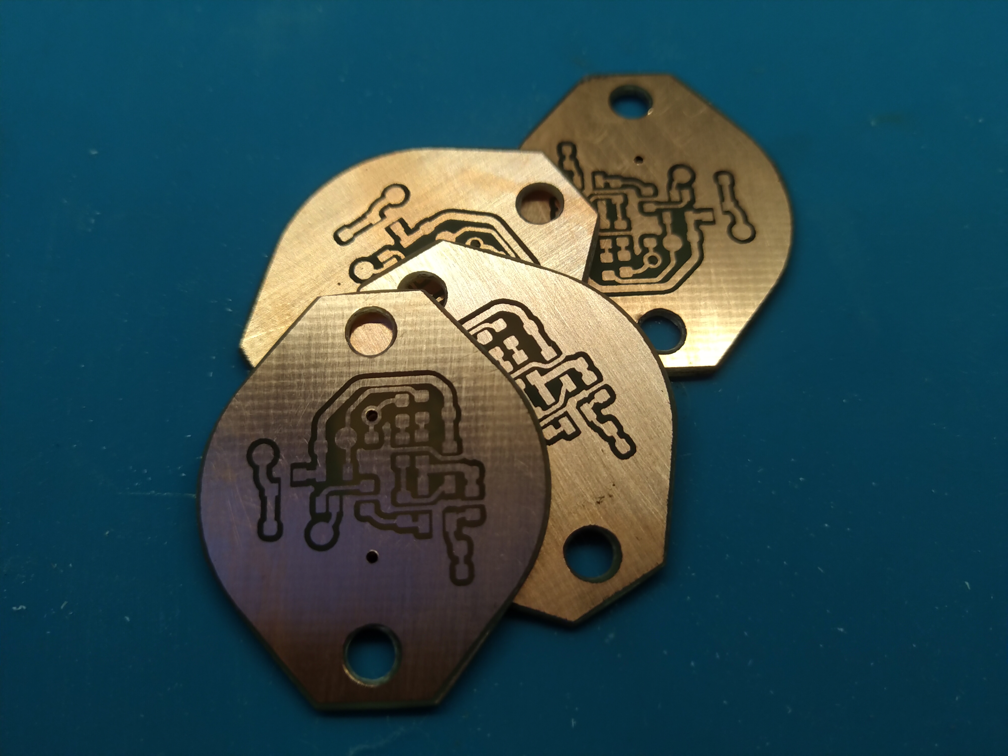
Documents/IMG_20230122_133305.jpg
