Maniak003/Anemometer/Documents/IMG_20230122_155250.jpg

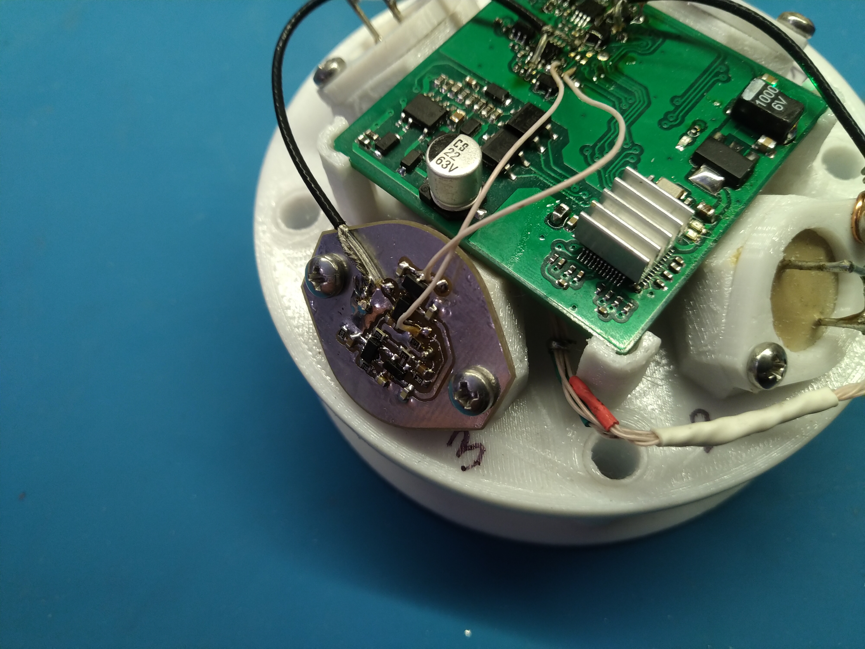
Documents/IMG_20230122_155250.jpg
