Maniak003/Anemometer/Documents/IMG_20230122_182952.jpg

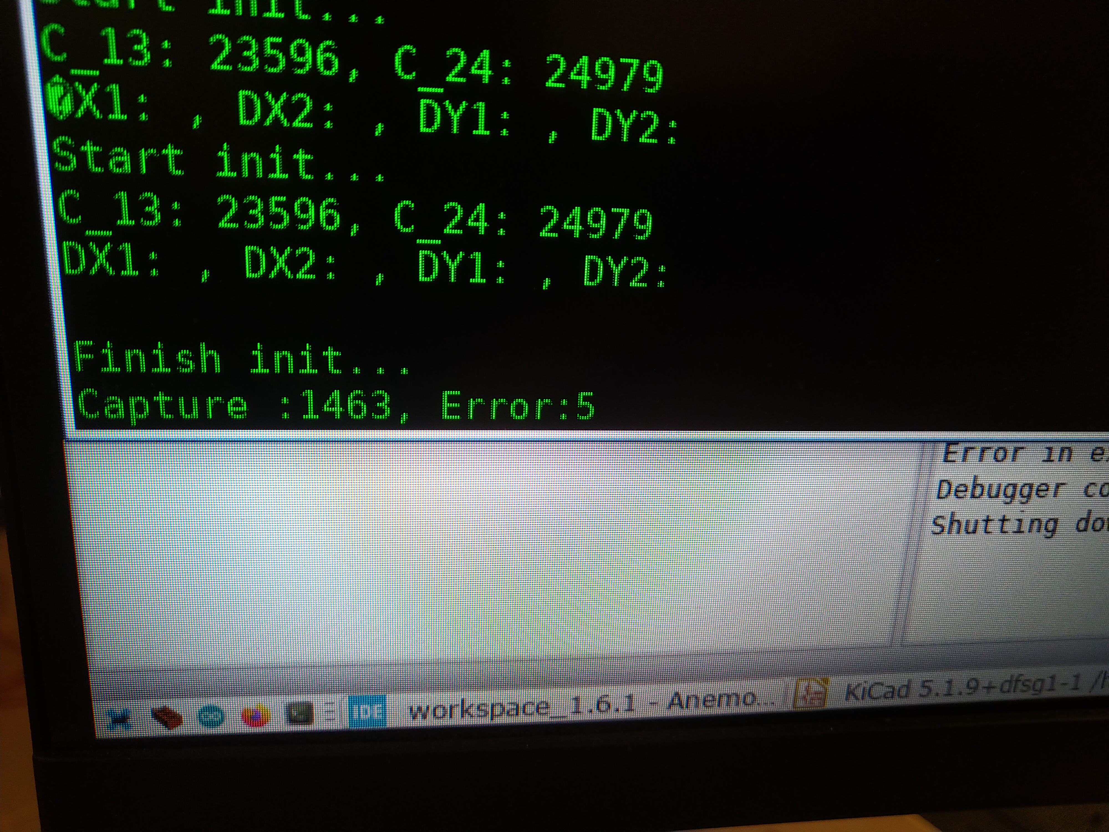
Documents/IMG_20230122_182952.jpg
