Maniak003/Anemometer/Documents/IMG_20230207_203821.jpg

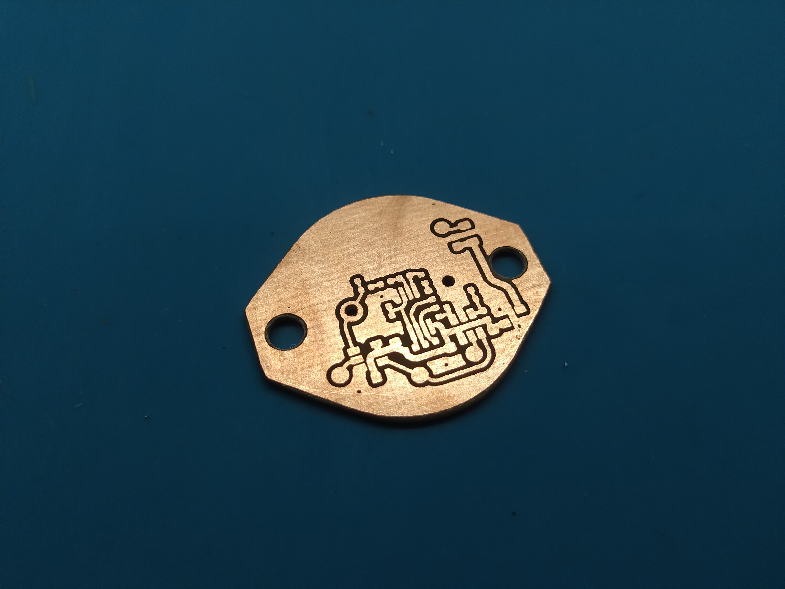
Documents/IMG_20230207_203821.jpg
