Maniak003/Anemometer/Documents/IMG_20230223_191301.jpg

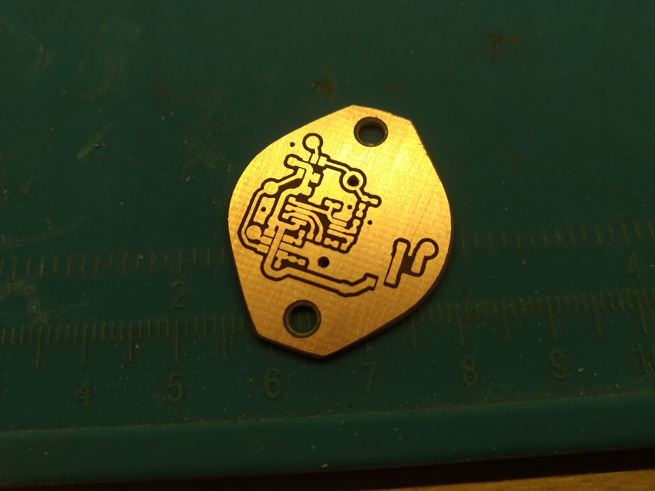
Documents/IMG_20230223_191301.jpg
