Maniak003/Anemometer/Documents/IMG_20230223_204826.jpg

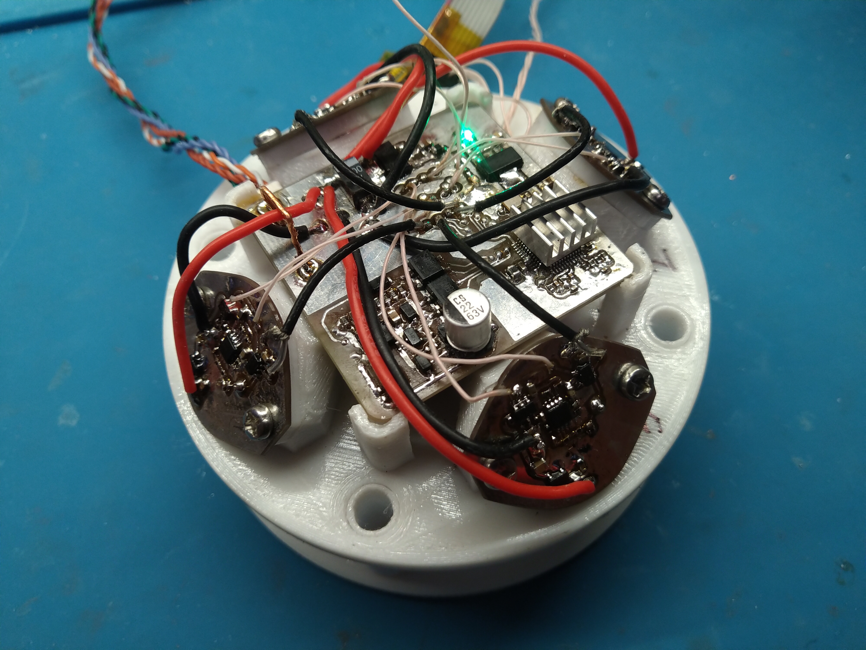
Documents/IMG_20230223_204826.jpg
