Maniak003/Anemometer/Documents/IMG_20230223_213639.jpg

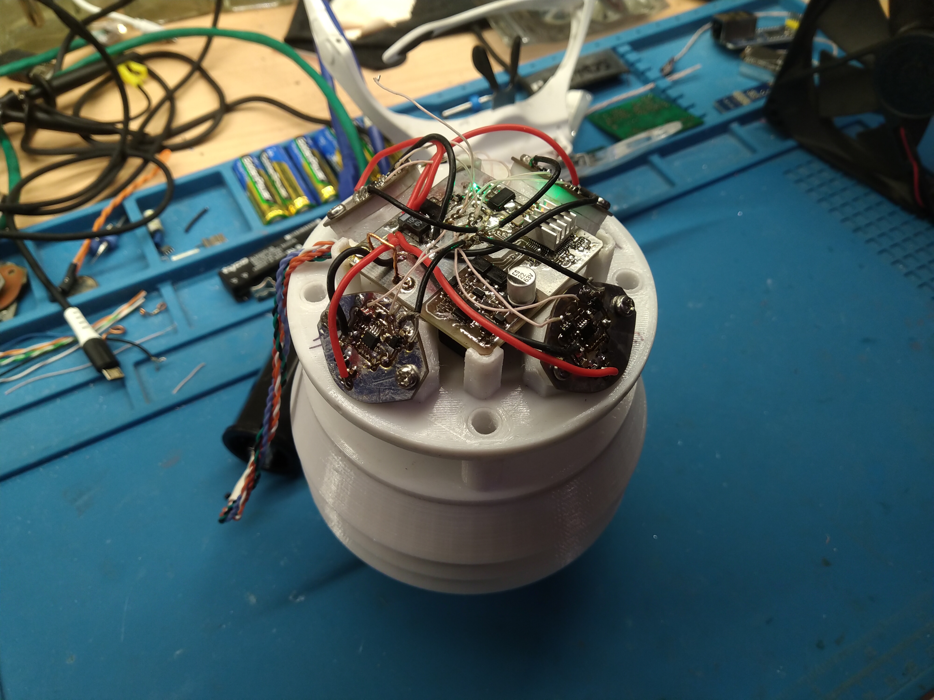
Documents/IMG_20230223_213639.jpg
