Maniak003/Anemometer/Documents/IMG_20230403_165320.jpg

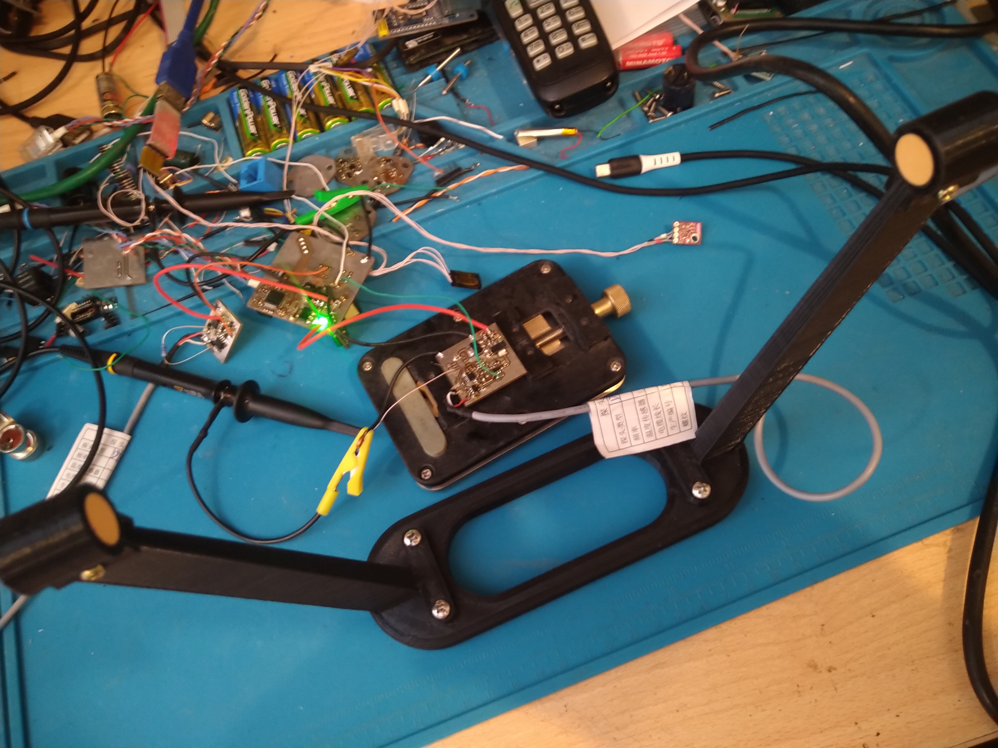
Documents/IMG_20230403_165320.jpg
