Maniak003/Anemometer/Documents/jitter-02.png

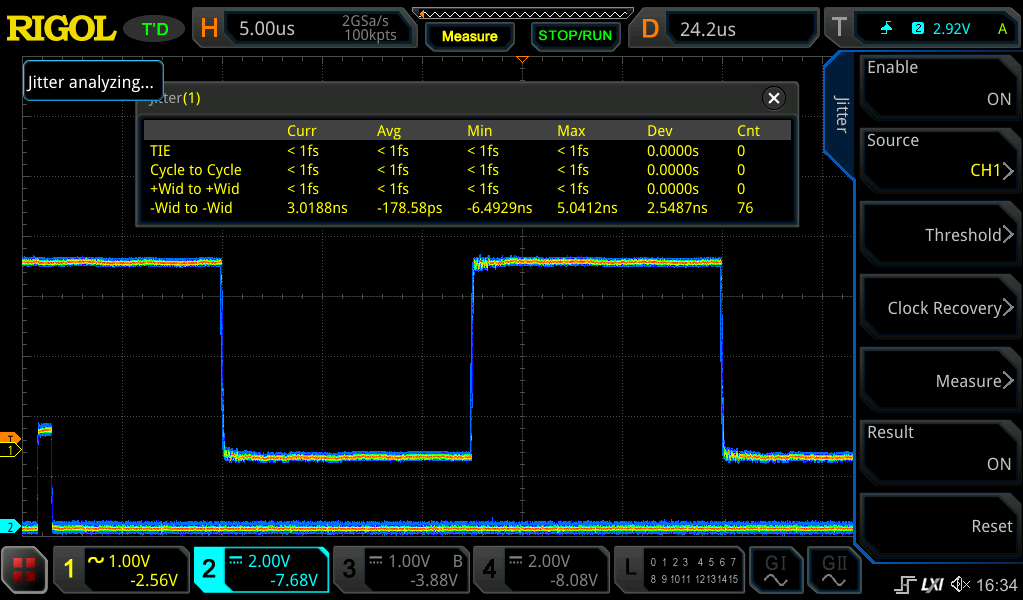
Documents/jitter-02.png
