Maniak003/Anemometer/Documents/jitter-03.png

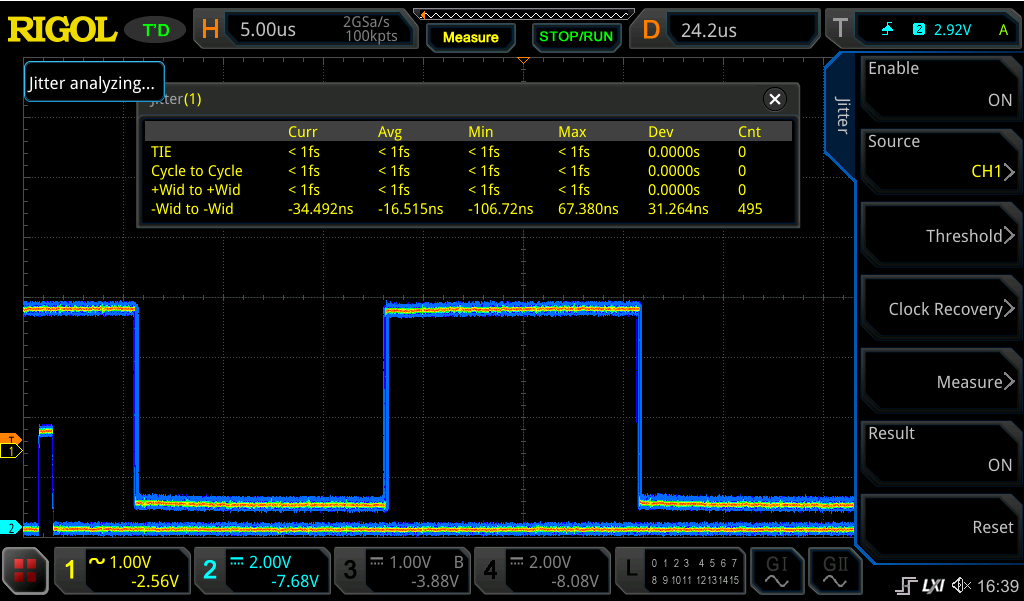
Documents/jitter-03.png
