Maniak003/Anemometer/Documents/pic_126_1.jpg

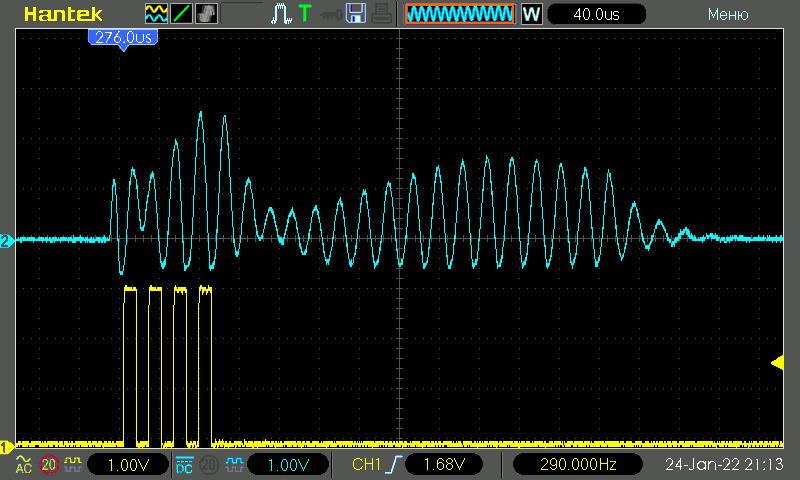
Documents/pic_126_1.jpg
