Maniak003/Anemometer/Documents/pic_126_2.jpg

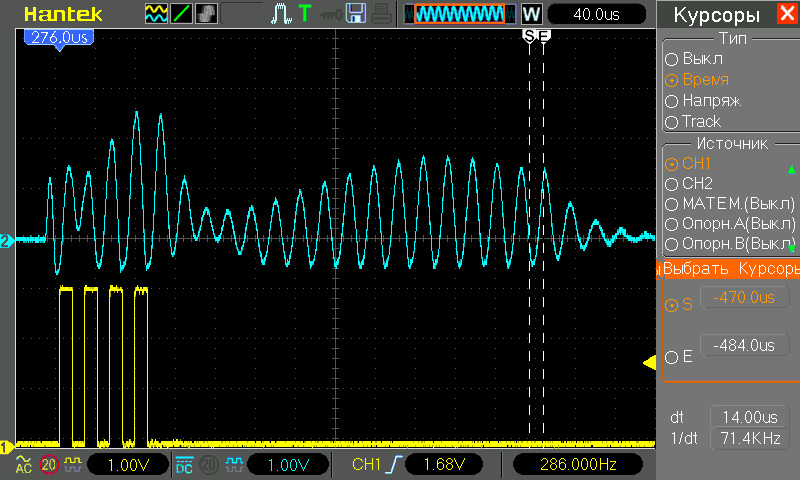
Documents/pic_126_2.jpg
