Maniak003/Anemometer/Documents/pic_126_4.jpg

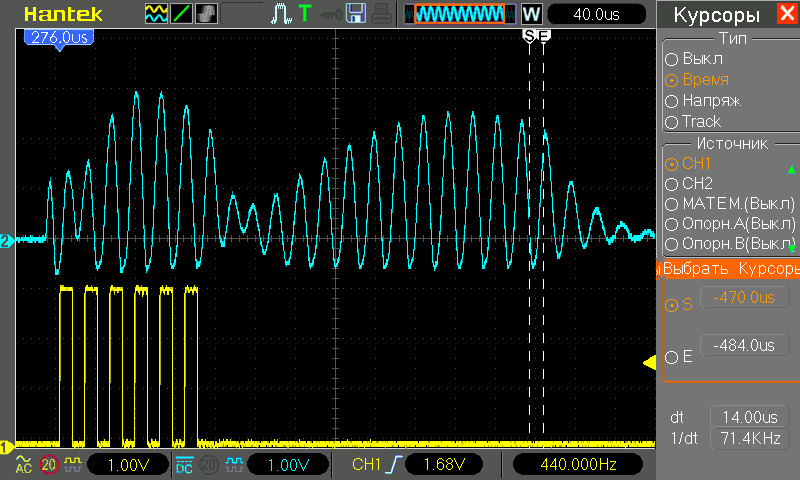
Documents/pic_126_4.jpg
