Maniak003/Anemometer/Documents/pic_127_1.jpg

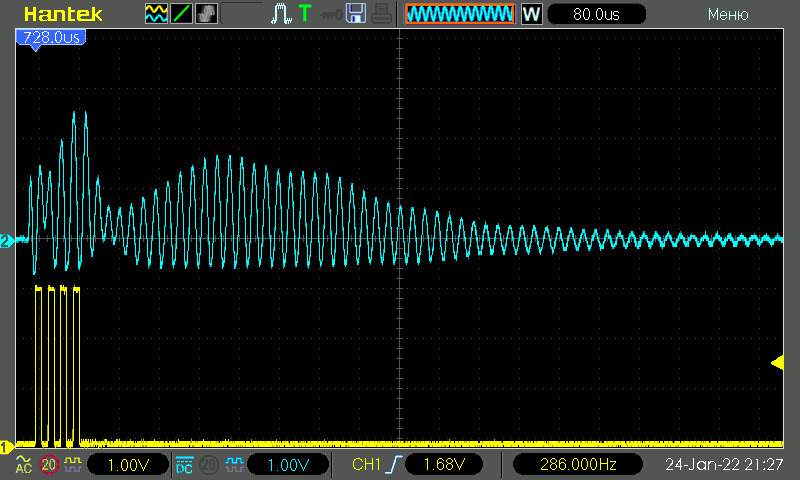
Documents/pic_127_1.jpg
