Maniak003/Anemometer/Documents/Screenshot_20220416-125117.png

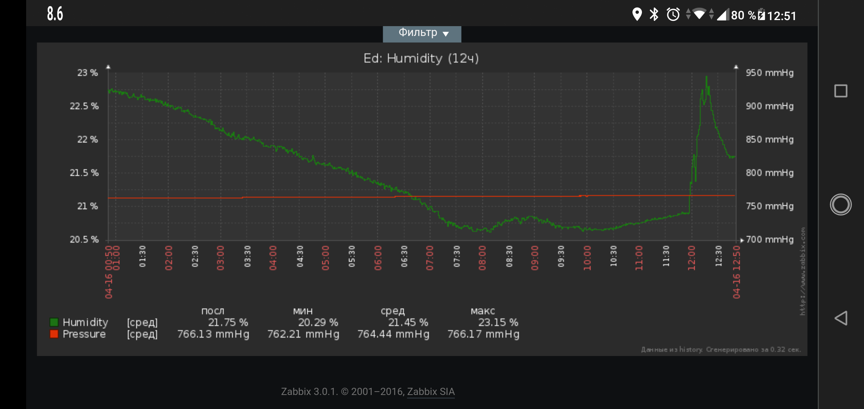
Documents/Screenshot_20220416-125117.png
