Maniak003/Anemometer/Documents/SD4932B.png

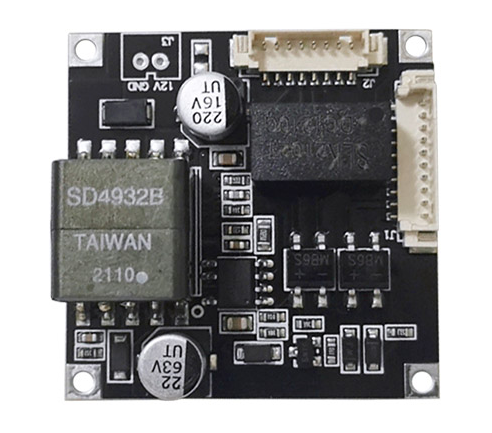
Documents/SD4932B.png
