Maniak003/Anemometer/Documents/TMP117.png

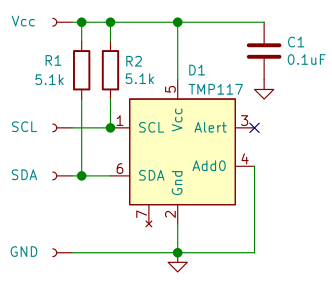
Documents/TMP117.png
