Maniak003/Anemometer/Documents/w5500_sch_v110.png

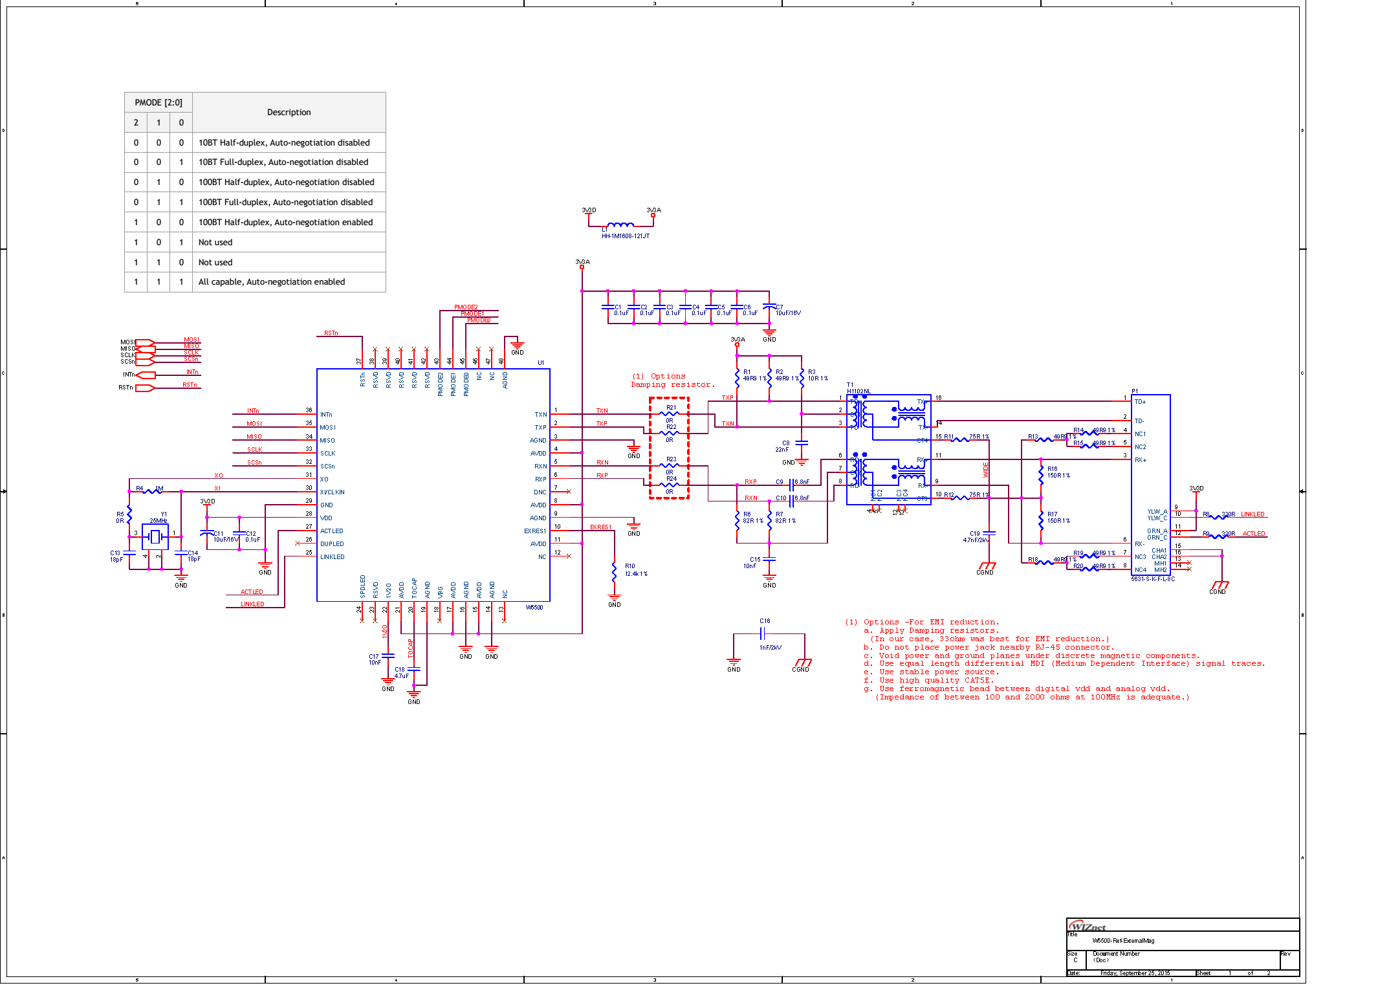
Documents/w5500_sch_v110.png
