Maniak003/Anemometer/Documents/zabbix.png

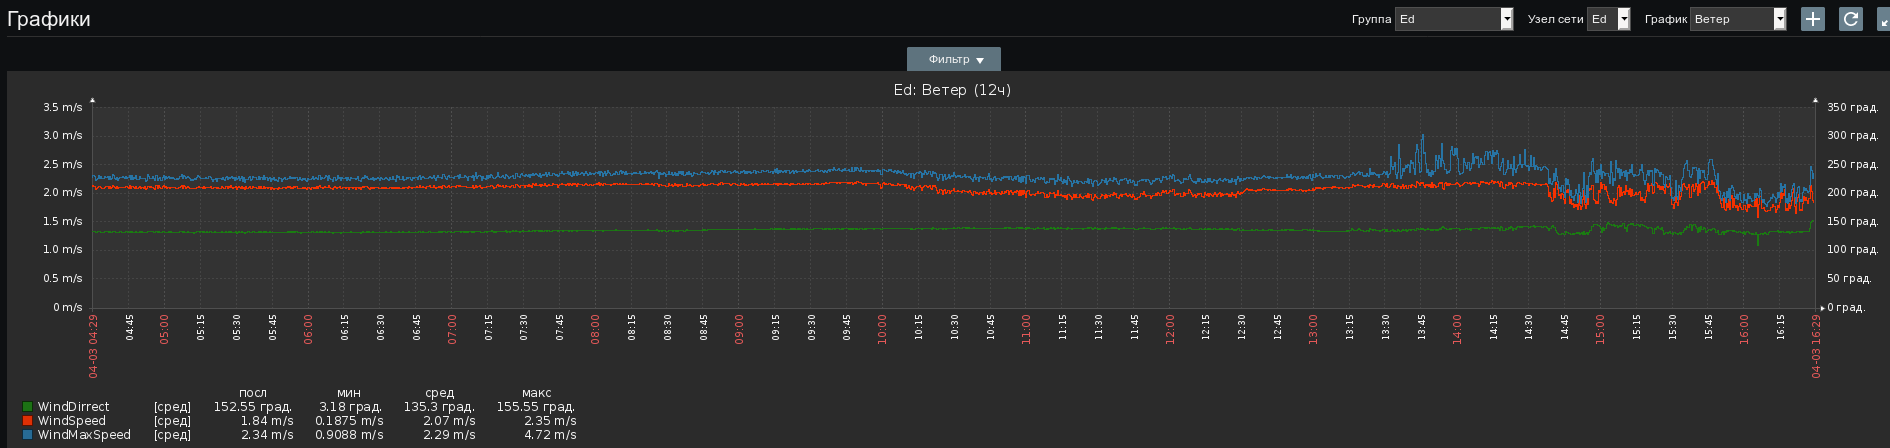
Documents/zabbix.png
