Maniak003/Anemometer/FreeCAD/base-4.FCStd

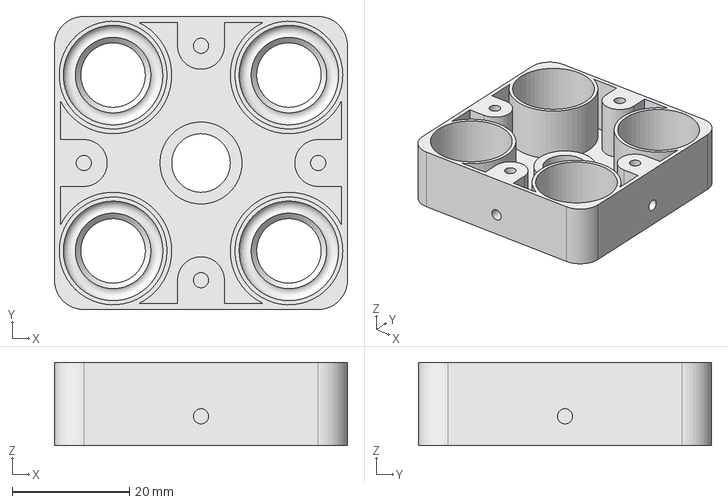
[picture p91: CAD file, 2022-03-30]
FreeCAD/base-4.FCStd
50.0 x 50.0 x 14.2 mm
