Maniak003/Anemometer/FreeCAD/base-3.FCStd

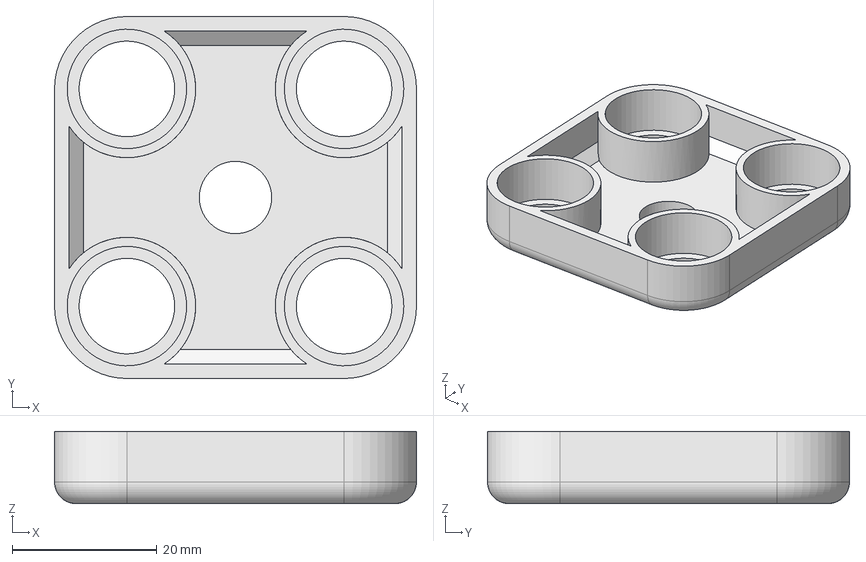
[picture p92: CAD file, 2022-01-16]
FreeCAD/base-3.FCStd
50.0 x 50.0 x 10.0 mm
