Maniak003/Anemometer/stm32cubeide/Anemometer_G474CBT6_MATLAB/Core/Inc/main.h

#define CONVERSION_COUNT 1024
#define MEASURE_COUNT 16
#define REF_COUNT 140
#define START_TEXT "\n\rAnemometr200 init\n\r"
#define FINISH_TEXT "Init finish.\n\r"
#define ERROR_TEXT "Error, system reset\n\r"
#define BME280_INIT_TEXT "BM280 init.."
#define AD5245_INIT_TEXT "AD5245 init.\n\r"
#define W5500_INIT_TEXT "W5500 init.."
#define ADC_TMR_INIT_TEXT "ADC, TMRs init.."
#define INIT_OK "Ok\n\r"
#define AD5245 /* Автоматическая регулировка уровня от 0 до 254 */
#define ACURACY_LEVEL 50
#define ADC_RESOLUTION 1024
#define NOMINAL_LEVEL 250 //450
#define MEASURMENT_DELAY 40200
#define DISTANCE 203.5f
#define ABS_ZERRO 273.15f
#define SAMPLE_RATE 1.0f / (170.0f / 4.0f) * (2.5f + 10.5f)
#define LED_PULSE HAL_GPIO_WritePin(LED_GPIO_Port, LED_Pin, GPIO_PIN_SET); HAL_GPIO_WritePin(LED_GPIO_Port, LED_Pin, GPIO_PIN_RESET);
#define LED_Pin GPIO_PIN_13
#define LED_GPIO_Port GPIOC
#define W5500_RST_Pin GPIO_PIN_3
#define W5500_RST_GPIO_Port GPIOA
#define W5500_CS_Pin GPIO_PIN_4
#define W5500_CS_GPIO_Port GPIOA
#define W5500_SCK_Pin GPIO_PIN_5
#define W5500_SCK_GPIO_Port GPIOA
#define W5500_MISO_Pin GPIO_PIN_6
#define W5500_MISO_GPIO_Port GPIOA
#define W5500_MOSI_Pin GPIO_PIN_7
#define W5500_MOSI_GPIO_Port GPIOA
#define AIn_Pin GPIO_PIN_0
#define AIn_GPIO_Port GPIOB
#define selZ1_Pin GPIO_PIN_11
#define selZ1_GPIO_Port GPIOB
#define selZ2_Pin GPIO_PIN_12
#define selZ2_GPIO_Port GPIOB
#define selZ3_Pin GPIO_PIN_13
#define selZ3_GPIO_Port GPIOB
#define selZ4_Pin GPIO_PIN_14
#define selZ4_GPIO_Port GPIOB
#define Z1_Pin GPIO_PIN_8
#define Z1_GPIO_Port GPIOA
#define Z2_Pin GPIO_PIN_9
#define Z2_GPIO_Port GPIOA
#define Z3_Pin GPIO_PIN_10
#define Z3_GPIO_Port GPIOA
#define Z4_Pin GPIO_PIN_11
#define Z4_GPIO_Port GPIOA
#define SCL_Pin GPIO_PIN_15
#define SCL_GPIO_Port GPIOA
#define TX_Pin GPIO_PIN_6
#define TX_GPIO_Port GPIOB
#define RX_Pin GPIO_PIN_7
#define RX_GPIO_Port GPIOB
#define SDA_Pin GPIO_PIN_9
#define SDA_GPIO_Port GPIOB
#define DHCP_SOCKET     0
#define DNS_SOCKET      1
#define TCP_SOCKET		2
#define DATA_BUF_SIZE   1024
#define ZABBIXAGHOST	"Anemometer04"  // Default hostname.
#define ZABBIXPORT		10051
#define ZABBIXMAXLEN	128
#define MAC_ADDRESS		0x00, 0x11, 0x22, 0x33, 0x44, 0xf0
