Maniak003/Anemometer/stm32cubeide/Anemometer_G474CBT6_MATLAB/Core/Src/maxEnvHilbert.c

/*
 * File: maxEnvHilbert.c
 *
 * MATLAB Coder version            : 5.5
 * C/C++ source code generated on  : 27-May-2023 12:28:36
 */

/* Include Files */
#include "maxEnvHilbert.h"
#include "FFTImplementationCallback.h"
#include "rt_nonfinite.h"
#include "spline.h"
#include "rt_nonfinite.h"
#include <math.h>
#include <string.h>

/* Function Declarations */
static float rt_hypotd_snf(float u0, float u1);

/* Function Definitions */
/*
 * Arguments    : double u0
 *                double u1
 * Return Type  : double
 */
static float rt_hypotd_snf(float u0, float u1)
{
	float a;
	float b;
	float y;
  a = fabs(u0);
  b = fabs(u1);
  if (a < b) {
    a /= b;
    y = b * sqrt(a * a + 1.0);
  } else if (a > b) {
    b /= a;
    y = a * sqrt(b * b + 1.0);
  } else if (rtIsNaN(b)) {
    y = rtNaN;
  } else {
    y = a * 1.4142135623730951;
  }
  return y;
}

/*
 * Arguments    : const double A[1024]
 *                const double B[140]
 * Return Type  : double
 */
float maxEnvHilbert(const float A[1024], const float B[140])
{
  static const float dv[513] = {1.0,
                                 0.99998117528260111,
                                 0.9999247018391445,
                                 0.9998305817958234,
                                 0.99969881869620425,
                                 0.99952941750109314,
                                 0.99932238458834954,
                                 0.99907772775264536,
                                 0.99879545620517241,
                                 0.99847558057329477,
                                 0.99811811290014918,
                                 0.99772306664419164,
                                 0.99729045667869021,
                                 0.99682029929116567,
                                 0.996312612182778,
                                 0.99576741446765982,
                                 0.99518472667219693,
                                 0.99456457073425542,
                                 0.99390697000235606,
                                 0.9932119492347945,
                                 0.99247953459871,
                                 0.99170975366909953,
                                 0.99090263542778,
                                 0.99005821026229712,
                                 0.989176509964781,
                                 0.98825756773074946,
                                 0.98730141815785843,
                                 0.98630809724459867,
                                 0.98527764238894122,
                                 0.984210092386929,
                                 0.98310548743121629,
                                 0.98196386910955524,
                                 0.98078528040323043,
                                 0.97956976568544052,
                                 0.97831737071962765,
                                 0.97702814265775439,
                                 0.97570213003852857,
                                 0.97433938278557586,
                                 0.97293995220556018,
                                 0.97150389098625178,
                                 0.970031253194544,
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
  static const float dv1[513] = {0.0,
                                  0.0061358846491544753,
                                  0.012271538285719925,
                                  0.01840672990580482,
                                  0.024541228522912288,
                                  0.030674803176636626,
                                  0.036807222941358832,
                                  0.04293825693494082,
                                  0.049067674327418015,
                                  0.055195244349689941,
                                  0.061320736302208578,
                                  0.067443919563664051,
                                  0.073564563599667426,
                                  0.079682437971430126,
                                  0.0857973123444399,
                                  0.091908956497132724,
                                  0.0980171403295606,
                                  0.10412163387205459,
                                  0.11022220729388306,
                                  0.11631863091190475,
                                  0.1224106751992162,
                                  0.12849811079379317,
                                  0.13458070850712617,
                                  0.14065823933284921,
                                  0.14673047445536175,
                                  0.15279718525844344,
                                  0.15885814333386145,
                                  0.16491312048996992,
                                  0.17096188876030122,
                                  0.17700422041214875,
                                  0.18303988795514095,
                                  0.18906866414980619,
                                  0.19509032201612825,
                                  0.2011046348420919,
                                  0.20711137619221856,
                                  0.21311031991609136,
                                  0.2191012401568698,
                                  0.22508391135979283,
                                  0.23105810828067111,
                                  0.2370236059943672,
                                  0.24298017990326387,
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
  creal_T b_x[1024];
  creal_T x[1024];
  float y_data[1034];
  float z[1024];
  float D[29];
  float n[29];
  float m;
  float mx;
  float mx2;
  float temp_im;
  float temp_re;
  float temp_re_tmp;
  float twid_re;
  int y_size[2];
  int b_k;
  int i;
  int iheight;
  int iy;
  int j;
  int ju;
  int k;
  mx = 0.0;
  mx2 = 0.0;
  m = 0.0;
  k = 0;
  memset(&z[0], 0, 1024U * sizeof(float));
  for (b_k = 0; b_k < 70; b_k++) {
    iheight = b_k + 953;
    for (iy = 0; iy <= iheight; iy++) {
      z[iy] += B[b_k] * A[(iy - b_k) + 70];
    }
  }
  for (b_k = 0; b_k < 70; b_k++) {
    iheight = 1023 - b_k;
    for (iy = 0; iy <= iheight; iy++) {
      ju = b_k + iy;
      z[ju] += B[b_k + 70] * A[iy];
    }
  }
  c_FFTImplementationCallback_doH(z, x);
  for (i = 0; i < 511; i++) {
    x[i + 1].re *= 2.0;
    x[i + 1].im *= 2.0;
    x[i + 513].re = 0.0;
    x[i + 513].im = 0.0;
  }
  memcpy(&b_x[0], &x[0], 1024U * sizeof(creal_T));
  iy = 0;
  ju = 0;
  for (i = 0; i < 1023; i++) {
    boolean_T tst;
    x[iy] = b_x[i];
    iy = 1024;
    tst = true;
    while (tst) {
      iy >>= 1;
      ju ^= iy;
      tst = ((ju & iy) == 0);
    }
    iy = ju;
  }
  x[iy] = b_x[1023];
  for (i = 0; i <= 1022; i += 2) {
    temp_re_tmp = x[i + 1].re;
    temp_re = x[i + 1].im;
    temp_im = x[i].re;
    twid_re = x[i].im;
    x[i + 1].re = temp_im - temp_re_tmp;
    x[i + 1].im = twid_re - temp_re;
    x[i].re = temp_im + temp_re_tmp;
    x[i].im = twid_re + temp_re;
  }
  iy = 2;
  ju = 4;
  b_k = 256;
  iheight = 1021;
  while (b_k > 0) {
    int b_temp_re_tmp;
    int istart;
    for (i = 0; i < iheight; i += ju) {
      b_temp_re_tmp = i + iy;
      temp_re = x[b_temp_re_tmp].re;
      temp_im = x[b_temp_re_tmp].im;
      x[b_temp_re_tmp].re = x[i].re - temp_re;
      x[b_temp_re_tmp].im = x[i].im - temp_im;
      x[i].re += temp_re;
      x[i].im += temp_im;
    }
    istart = 1;
    for (j = b_k; j < 512; j += b_k) {
      double twid_im;
      int ihi;
      twid_re = dv[j];
      twid_im = dv1[j];
      i = istart;
      ihi = istart + iheight;
      while (i < ihi) {
        b_temp_re_tmp = i + iy;
        temp_re_tmp = x[b_temp_re_tmp].im;
        temp_im = x[b_temp_re_tmp].re;
        temp_re = twid_re * temp_im - twid_im * temp_re_tmp;
        temp_im = twid_re * temp_re_tmp + twid_im * temp_im;
        x[b_temp_re_tmp].re = x[i].re - temp_re;
        x[b_temp_re_tmp].im = x[i].im - temp_im;
        x[i].re += temp_re;
        x[i].im += temp_im;
        i += ju;
      }
      istart++;
    }
    b_k /= 2;
    iy = ju;
    ju += ju;
    iheight -= iy;
  }
  for (i = 0; i < 1024; i++) {
    temp_im = 0.0009765625 * x[i].re;
    temp_re = 0.0009765625 * x[i].im;
    x[i].re = temp_im;
    x[i].im = temp_re;
    temp_im = rt_hypotd_snf(temp_im, temp_re);
    z[i] = temp_im;
    if (temp_im > m) {
      m = temp_im;
      mx = (float)i + 1.0;
    }
  }
  n[28] = mx + 5.0;
  n[0] = mx - 4.0;
  iy = (int)(((float)mx + 5.0F) - ((float)mx - 4.0F));
  temp_im = (float)iy / 28.0;
  for (b_k = 0; b_k < 27; b_k++) {
    n[b_k + 1] = (mx - 4.0) + ((float)b_k + 1.0) * temp_im;
  }
  if (mx + 5.0 < mx - 4.0) {
    y_size[0] = 1;
    y_size[1] = 0;
  } else {
    y_size[0] = 1;
    y_size[1] = iy + 1;
    for (iheight = 0; iheight <= iy; iheight++) {
      y_data[iheight] = (mx - 4.0) + (float)iheight;
    }
  }
  spline(y_data, y_size, &z[(int)mx + -5], n, D);
  for (i = 0; i < 29; i++) {
    temp_im = D[i];
    if (temp_im > mx2) {
      mx2 = temp_im;
      k = i + 1;
    }
  }
  return (mx - 4.0) + ((float)k - 1.0) / 3.0;
}

/*
 * File trailer for maxEnvHilbert.c
 *
 * [EOF]
 */
