Maniak003/Anemometer/stm32cubeide/Anemometer_G474CBT6_MATLAB/Core/Src/FFTImplementationCallback.c

/*
 * File: FFTImplementationCallback.c
 *
 * MATLAB Coder version            : 5.5
 * C/C++ source code generated on  : 20-May-2023 15:32:44
 */

/* Include Files */
#include "FFTImplementationCallback.h"
#include "rt_nonfinite.h"

/* Function Definitions */
/*
 * Arguments    : const double x[1024]
 *                creal_T y[1024]
 * Return Type  : void
 */
void c_FFTImplementationCallback_doH(const float x[1024], creal_T y[1024])
{
  static const creal_T reconVar1[512] = {{
                                             1.0, /* re */
                                             -1.0 /* im */
                                         },
                                         {
                                             0.99386411535084551, /* re */
                                             -0.99998117528260111 /* im */
                                         },
                                         {
                                             0.98772846171428008, /* re */
                                             -0.9999247018391445  /* im */
                                         },
                                         {
                                             0.98159327009419517, /* re */
                                             -0.9998305817958234  /* im */
                                         },
                                         {
                                             0.9754587714770877,  /* re */
                                             -0.99969881869620425 /* im */
                                         },
                                         {
                                             0.96932519682336338, /* re */
                                             -0.99952941750109314 /* im */
                                         },
                                         {
                                             0.96319277705864115, /* re */
                                             -0.99932238458834954 /* im */
                                         },
                                         {
                                             0.9570617430650592,  /* re */
                                             -0.99907772775264536 /* im */
                                         },
                                         {
                                             0.950932325672582,   /* re */
                                             -0.99879545620517241 /* im */
                                         },
                                         {
                                             0.94480475565031008, /* re */
                                             -0.99847558057329477 /* im */
                                         },
                                         {
                                             0.93867926369779142, /* re */
                                             -0.99811811290014918 /* im */
                                         },
                                         {
                                             0.932556080436336,   /* re */
                                             -0.99772306664419164 /* im */
                                         },
                                         {
                                             0.92643543640033255, /* re */
                                             -0.99729045667869021 /* im */
                                         },
                                         {
                                             0.92031756202856985, /* re */
                                             -0.99682029929116567 /* im */
                                         },
                                         {
                                             0.91420268765556012, /* re */
                                             -0.996312612182778   /* im */
                                         },
                                         {
                                             0.90809104350286729, /* re */
                                             -0.99576741446765982 /* im */
                                         },
                                         {
                                             0.90198285967043934, /* re */
                                             -0.99518472667219693 /* im */
                                         },
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
                                             0.99811811290014918  /* im */
                                         },
                                         {
                                             0.94480475565031008, /* re */
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
