Maniak003/Anemometer/stm32cubeide/Anemometer_G474CBT6_MATLAB/Core/Inc/maxEnvHilbert_data.h

/*
 * File: maxEnvHilbert_data.h
 *
 * MATLAB Coder version            : 5.5
 * C/C++ source code generated on  : 27-May-2023 12:28:36
 */

#ifndef MAXENVHILBERT_DATA_H
#define MAXENVHILBERT_DATA_H

/* Include Files */
#include "rtwtypes.h"
#include <stddef.h>
#include <stdlib.h>

#endif
/*
 * File trailer for maxEnvHilbert_data.h
 *
 * [EOF]
 */
