Maniak003/Anemometer/stm32cubeide/Anemometer_G474CBT6_MATLAB/Core/Inc/maxEnvHilbert.h

/*
 * File: maxEnvHilbert.h
 *
 * MATLAB Coder version            : 5.5
 * C/C++ source code generated on  : 27-May-2023 12:28:36
 */

#ifndef MAXENVHILBERT_H
#define MAXENVHILBERT_H

/* Include Files */
#include "rtwtypes.h"
#include <stddef.h>
#include <stdlib.h>

#ifdef __cplusplus
extern "C" {
#endif

/* Function Declarations */
extern float maxEnvHilbert(const float A[1024], const float B[140]);

#ifdef __cplusplus
}
#endif

#endif
/*
 * File trailer for maxEnvHilbert.h
 *
 * [EOF]
 */
