Maniak003/Anemometer/stm32cubeide/Anemometer_200_F303/Core/Inc/maxEnvHilbert_terminate.h

/*
 * File: maxEnvHilbert_terminate.h
 *
 * MATLAB Coder version            : 5.5
 * C/C++ source code generated on  : 29-Apr-2023 16:59:07
 */

#ifndef MAXENVHILBERT_TERMINATE_H
#define MAXENVHILBERT_TERMINATE_H

/* Include Files */
#include "rtwtypes.h"
#include <stddef.h>
#include <stdlib.h>

#ifdef __cplusplus
extern "C" {
#endif

/* Function Declarations */
extern void maxEnvHilbert_terminate(void);

#ifdef __cplusplus
}
#endif

#endif
/*
 * File trailer for maxEnvHilbert_terminate.h
 *
 * [EOF]
 */
