Maniak003/Anemometer/stm32cubeide/Anemometer_200_F303/Core/Src/maxEnvHilbert_terminate.c

/*
 * File: maxEnvHilbert_terminate.c
 *
 * MATLAB Coder version            : 5.5
 * C/C++ source code generated on  : 29-Apr-2023 16:59:07
 */

/* Include Files */
#include "maxEnvHilbert_terminate.h"
#include "rt_nonfinite.h"

/* Function Definitions */
/*
 * Arguments    : void
 * Return Type  : void
 */
void maxEnvHilbert_terminate(void)
{
}

/*
 * File trailer for maxEnvHilbert_terminate.c
 *
 * [EOF]
 */
